JoseSanchez122/MULTI_TIMERS_CALIBRATOR/Hardware_design/parts/3D/BUTTON_TL3301FF160QG.step

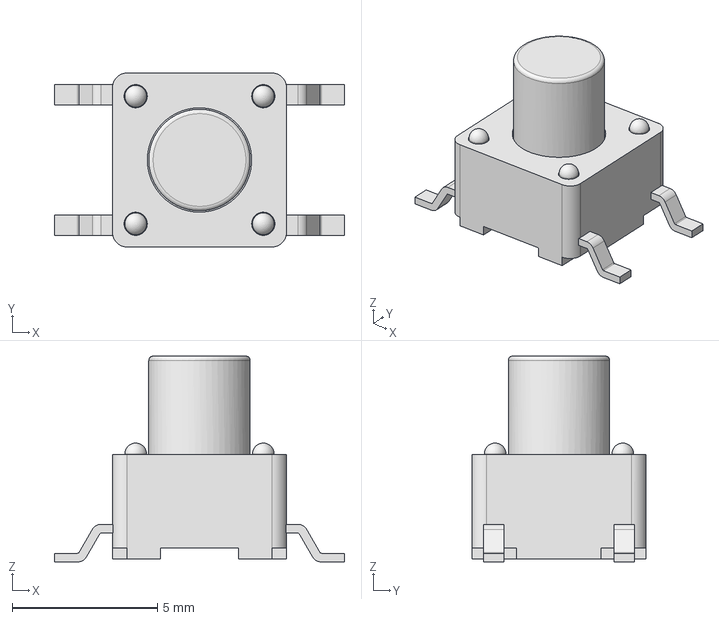
[picture p16: CAD file, 2026-05-31]
Hardware_design/parts/3D/BUTTON_TL3301FF160QG.step
10.0 x 6.00 x 7.10 mm
