JoseSanchez122/MULTI_TIMERS_CALIBRATOR/Hardware_design/parts/3D/V_REGU_LP3875EMP-3.3.step

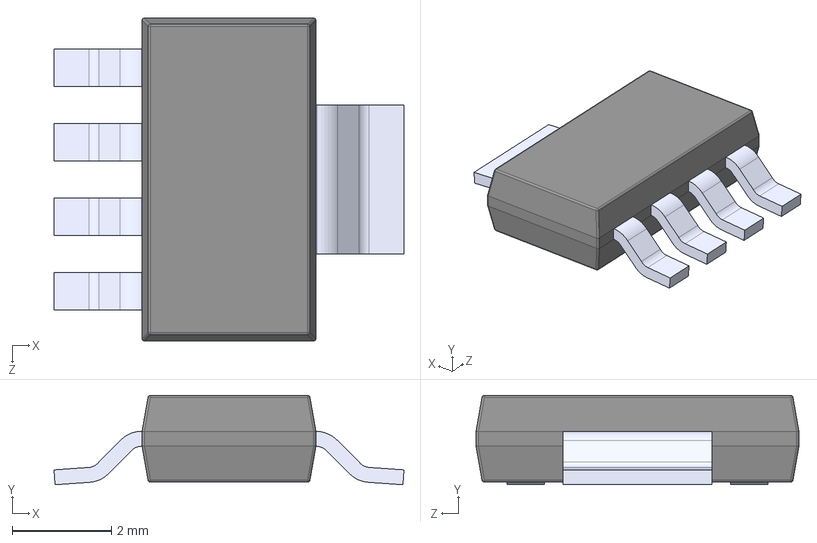
[picture p17: CAD file, 2026-05-31]
Hardware_design/parts/3D/V_REGU_LP3875EMP-3.3.step
7.04 x 1.80 x 6.50 mm
