JoseSanchez122/MULTI_TIMERS_CALIBRATOR/Hardware_design/parts/3D/LS7366R-S.step

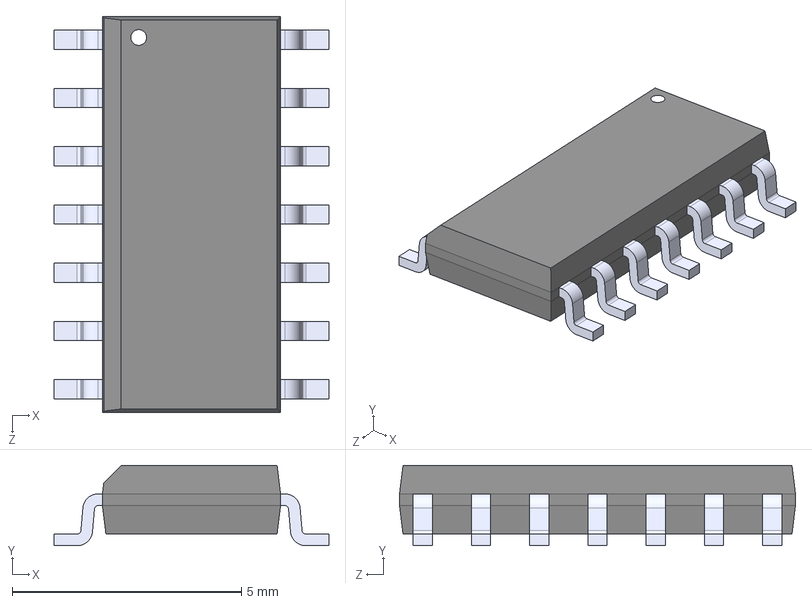
[picture p18: CAD file, 2026-05-31]
Hardware_design/parts/3D/LS7366R-S.step
5.99 x 1.75 x 8.64 mm
