JoseSanchez122/MULTI_TIMERS_CALIBRATOR/Hardware_design/parts/3D/POWER_CONE_54-00131.step

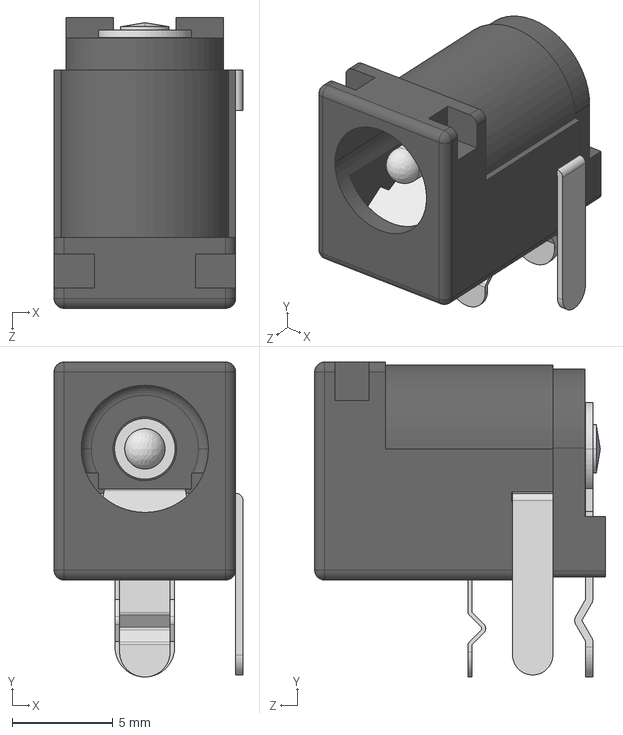
[picture p19: CAD file, 2026-05-31]
Hardware_design/parts/3D/POWER_CONE_54-00131.step
9.36 x 15.6 x 14.4 mm
