JoseSanchez122/MULTI_TIMERS_CALIBRATOR/Hardware_design/parts/3D/GREEN_LED_LTST-C170KGKT.step

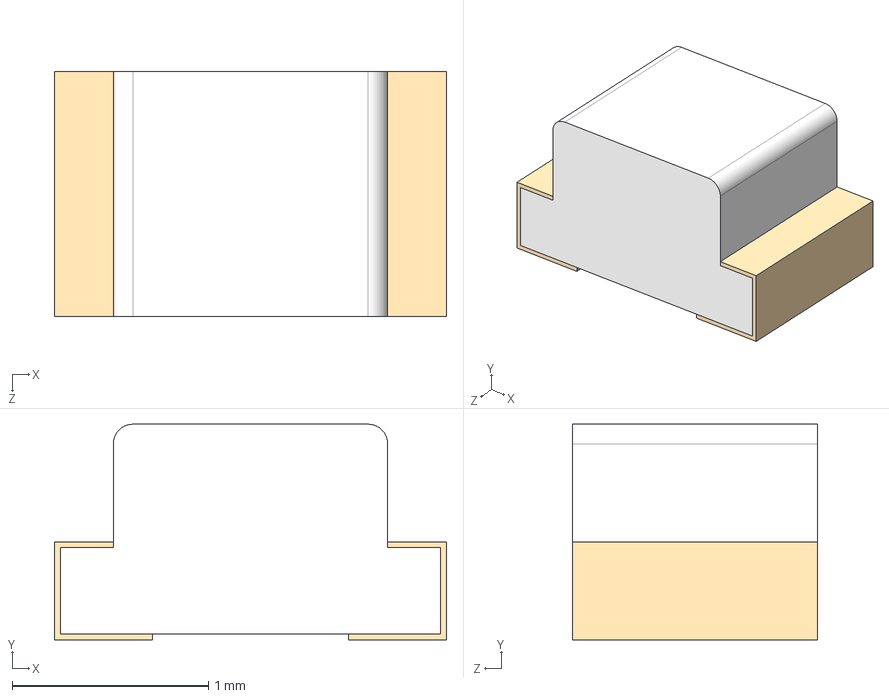
[picture p20: CAD file, 2026-05-31]
Hardware_design/parts/3D/GREEN_LED_LTST-C170KGKT.step
2.00 x 1.10 x 1.25 mm
