JoseSanchez122/MULTI_TIMERS_CALIBRATOR/Hardware_design/parts/3D/DEBOUNCE_CHIP_SN74LVC1G123DCTR.step

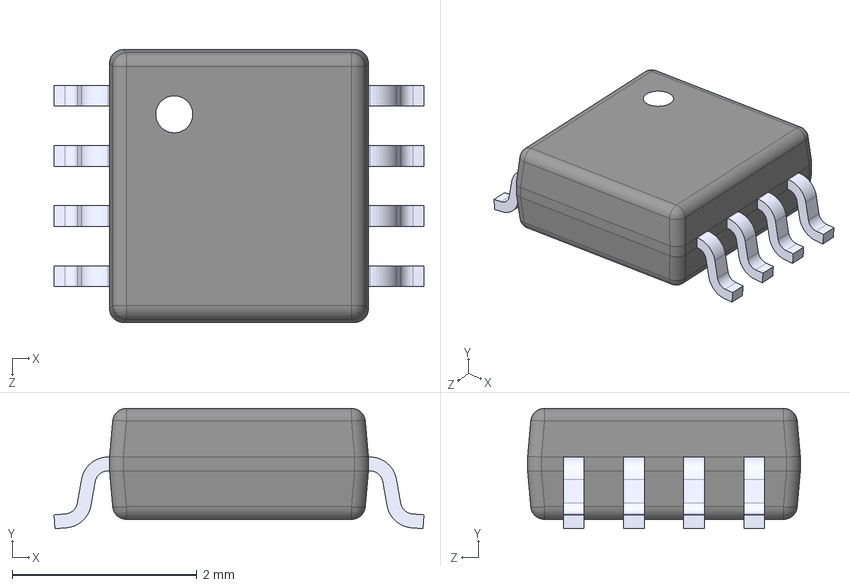
[picture p21: CAD file, 2026-05-31]
Hardware_design/parts/3D/DEBOUNCE_CHIP_SN74LVC1G123DCTR.step
4.00 x 1.30 x 2.95 mm
