JoseSanchez122/MULTI_TIMERS_CALIBRATOR/Hardware_design/parts/3D/PROG_CONECTOR_FTSH-103-01-F-D.step

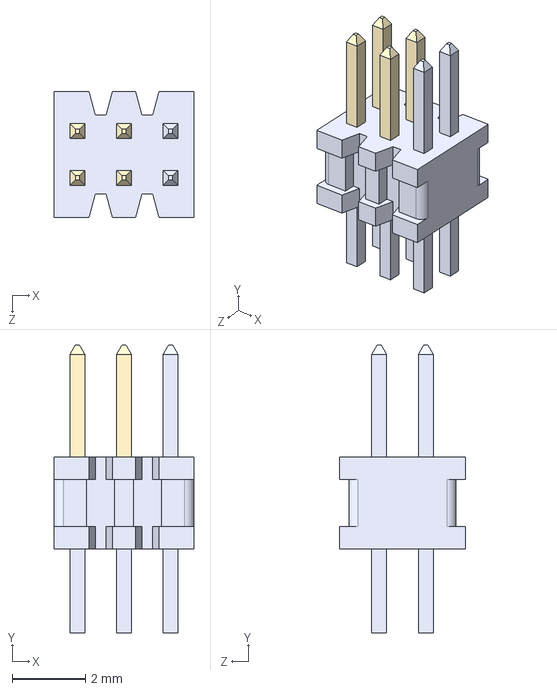
[picture p22: CAD file, 2026-05-31]
Hardware_design/parts/3D/PROG_CONECTOR_FTSH-103-01-F-D.step
3.81 x 7.85 x 3.43 mm
