JoseSanchez122/MULTI_TIMERS_CALIBRATOR/Hardware_design/parts/3D/ESP32-S3-WROOM-1-N16.stp

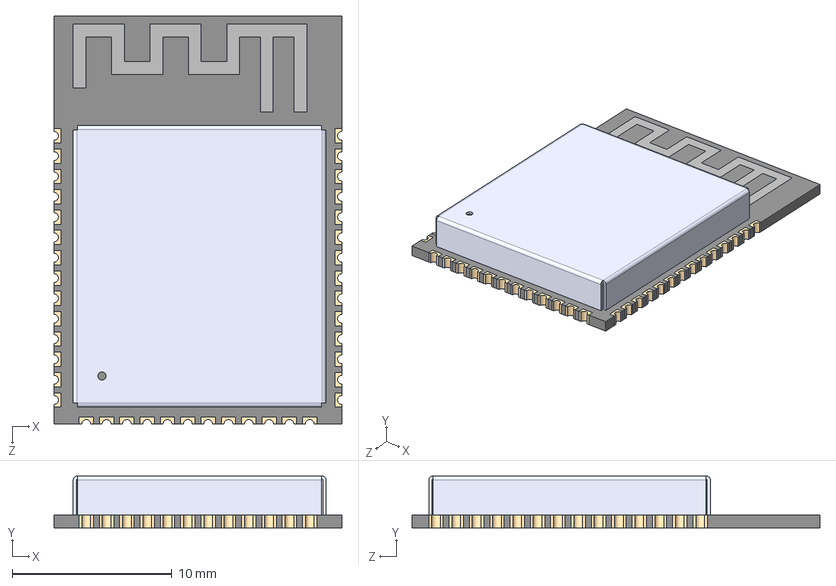
[picture p23: CAD file, 2026-05-30]
Hardware_design/parts/3D/ESP32-S3-WROOM-1-N16.stp
18.0 x 3.25 x 25.5 mm
