JoseSanchez122/MULTI_TIMERS_CALIBRATOR/Hardware_design/Hardware_design.kicad_pcb

## KiCad design Hardware_design/Hardware_design.kicad_pcb (2026-07-23)

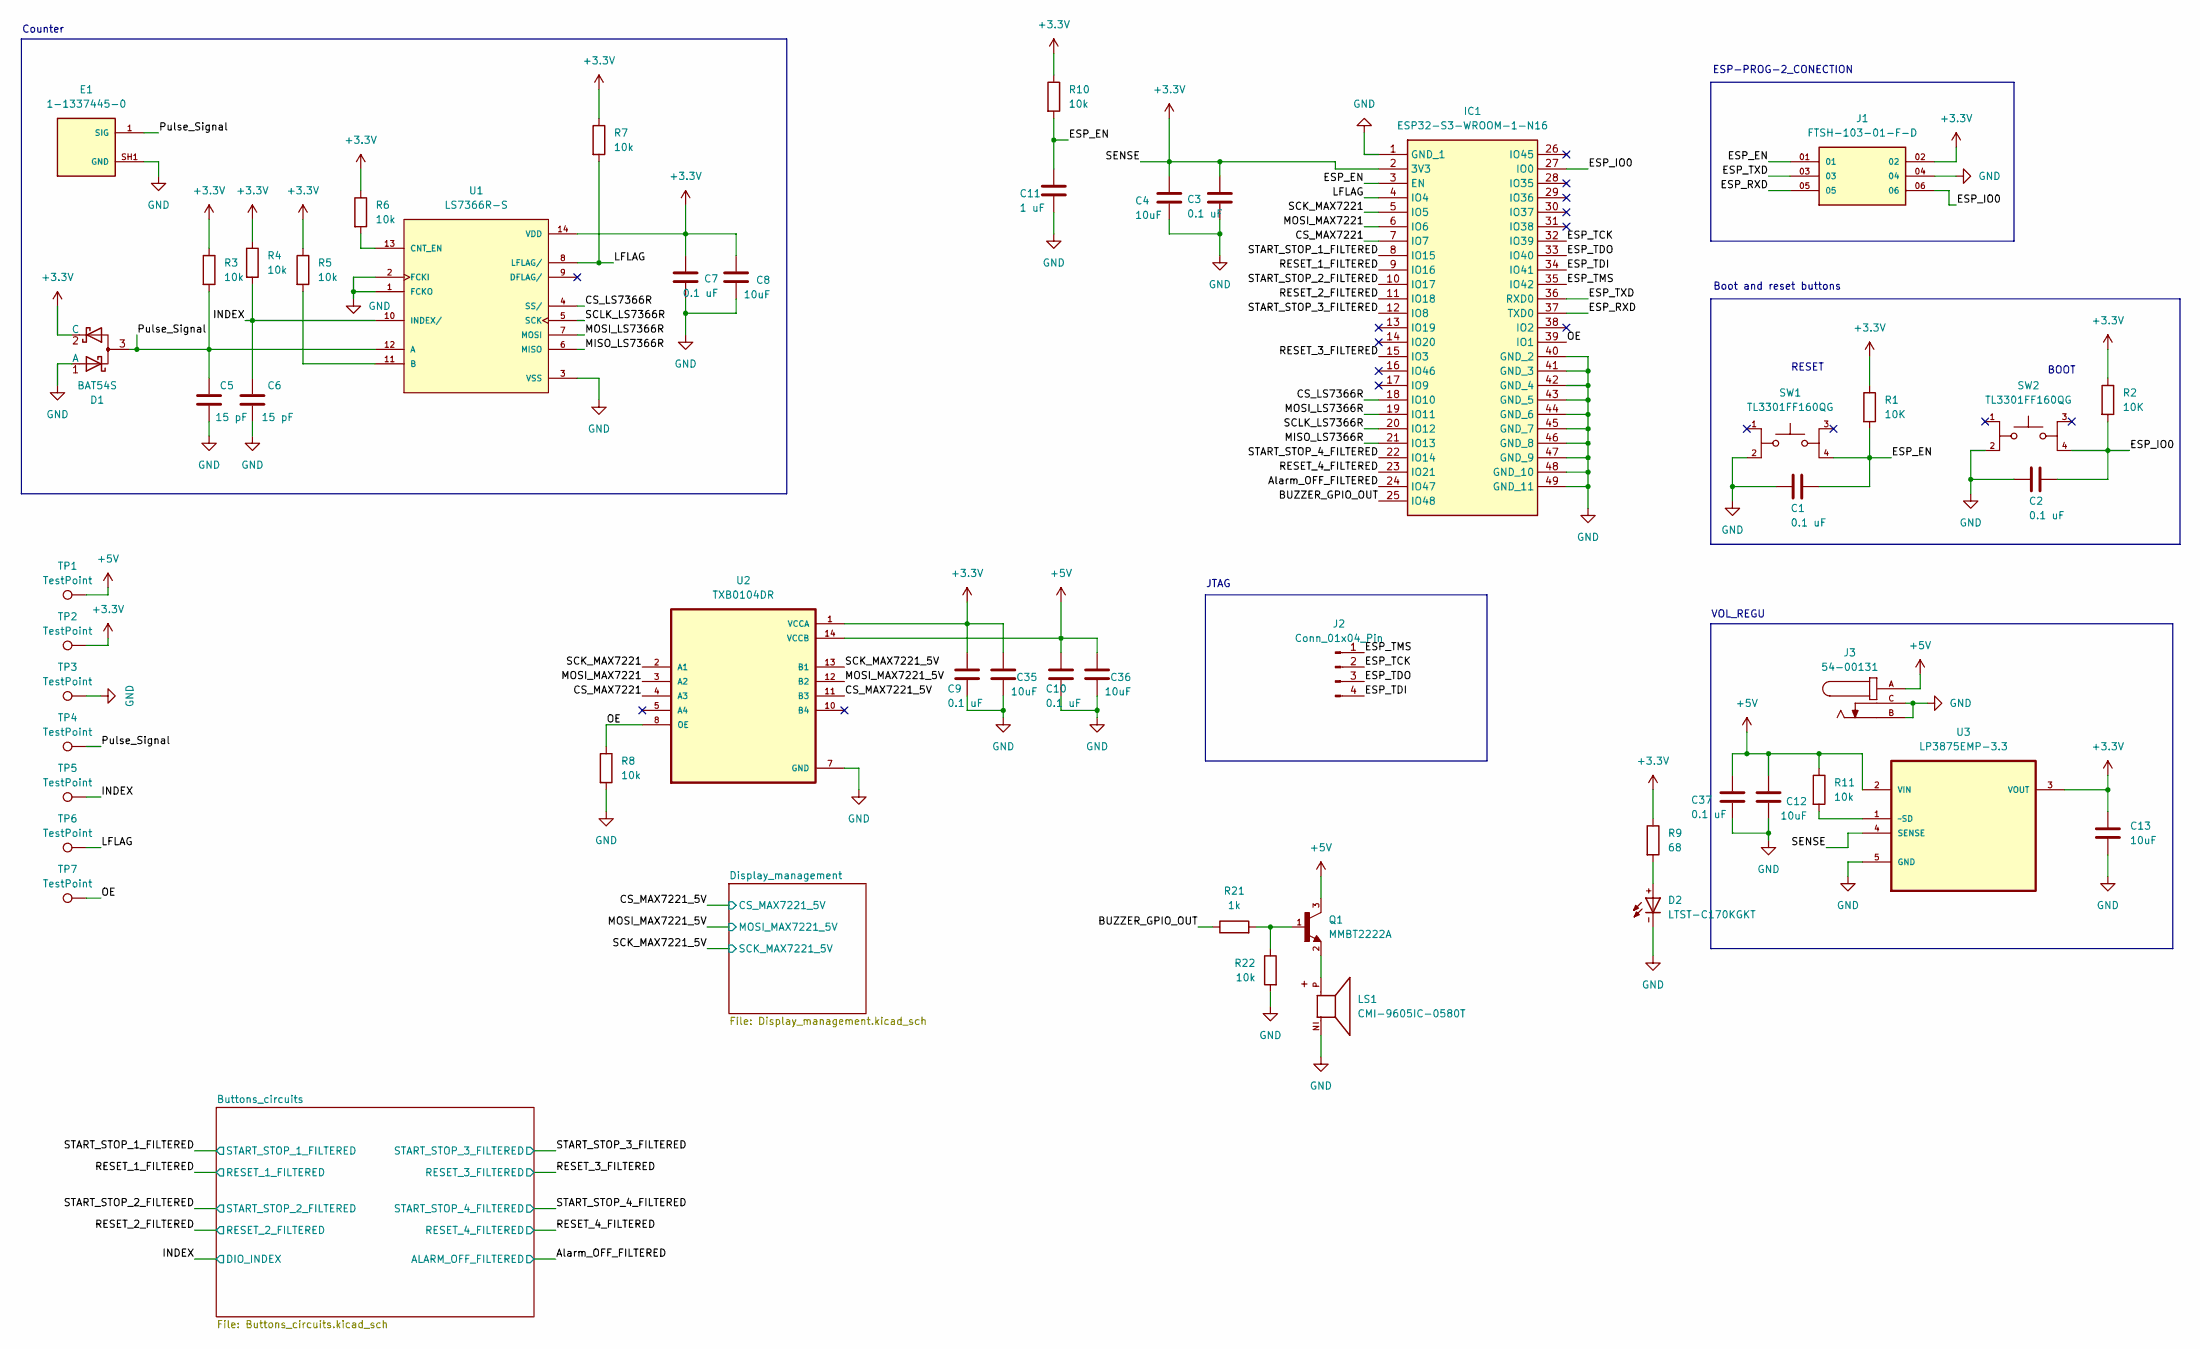
[picture p24: schematic Hardware_design.kicad_sch]

Parts:
C1, C2, C3, C7, C9, C10, C37: 0.1 uF; 0805_SMD_CERAMIC_CAP_T491B106K016AT
C4, C8, C12, C13, C35, C36: 10uF; 0805_SMD_TANT_CAP_T491B106K016AT
C5, C6: 15 pF; 0805_SMD_CERAMIC_CAP_T491B106K016AT
C11: 1 uF; CAP_0603_CAPC1608X90N
D1: BAT54S; Schottky_diode_BAT54S
D2: LTST-C170KGKT; GREEN_LED_LTST-C170KGKT; DigiKey_Part_Number 160-1414-1-ND
E1: 1-1337445-0; VNC_CONECTOR_1-1337445-0; PARTREV C
IC1: ESP32-S3-WROOM-1-N16; ESP32S3WROOM1N16; Mouser Part Number 356-ESP32S3WROOM1N16
J1: FTSH-103-01-F-D; PROG_CONECTOR_SAMTEC_FTSH-103-01-F-D; PARTREV B
J2: Conn_01x04_Pin; 4_pin_FTR-104-01-L-S
J3: 54-00131; POWER_CONE_54-00131; PARTREV A
LS1: CMI-9605IC-0580T; BUZZER_CMI-9605IC-0580T; PARTREV 1.0
Q1: MMBT2222A; TRANSISTOR_MMBT2222A; PARTREV 2024-03-11
R1, R2: 10K; 0805_RES_RESC2012X60N
R3, R4, R5, R6, R7, R8, R10, R11, R22: 10k; 0805_RES_RESC2012X60N
R9: 68; 0805_RES_RESC2012X60N
R21: 1k; 0805_RES_RESC2012X60N
SW1, SW2: TL3301FF160QG; BUTTON_TL3301FF160QG; PARTREV E
TP1, TP2, TP3, TP4, TP5, TP6, TP7: TestPoint; TestPoint_Pad_1.0x1.0mm
U1: LS7366R-S; PARTREV June 2014
U2: TXB0104DR; LEVEL_SHIFTER_TXB0104DR
U3: LP3875EMP-3.3; V_REGU_LP3875EMP-3.3; MPN LP3875EMP-3.3

Connections:
+3.3V: C3.1, C4.1, C7.1, C8.1, C9.1, C13.1, C35.1, D1.2 (C), IC1.2 (3V3), J1.02, R1.1, R2.1, R3.1, R4.1, R5.1, R6.1, R7.1, R9.1, R10.1, TP2.1 (1_1), U1.14 (VDD), U2.1 (VCCA), U3.3 (VOUT), U3.4 (SENSE); also elsewhere on the board
+5V: C10.1, C12.1, C36.1, C37.1, J3.A, Q1.3, R11.1, TP1.1 (1_1), U2.14 (VCCB), U3.2 (VIN); also elsewhere on the board
/Alarm_OFF_FILTERED: IC1.24 (IO47); also elsewhere on the board
/BUZZER_GPIO_OUT: IC1.25 (IO48), R21.1
/CS_LS7366R: IC1.18 (IO10), U1.4 (SS/)
/CS_MAX7221: IC1.7 (IO7), U2.4 (A3)
/CS_MAX7221_5V: U2.11 (B3); also elsewhere on the board
/ESP_EN: C1.1, C11.1, IC1.3 (EN), J1.01, R1.2, R10.2, SW1.4
/ESP_IO0: C2.1, IC1.27 (IO0), J1.06, R2.2, SW2.4
/ESP_RXD: IC1.37 (TXD0), J1.05
/ESP_TCK: IC1.32 (IO39), J2.2
/ESP_TDI: IC1.34 (IO41), J2.4
/ESP_TDO: IC1.33 (IO40), J2.3
/ESP_TMS: IC1.35 (IO42), J2.1
/ESP_TXD: IC1.36 (RXD0), J1.03
/INDEX: C6.1, R4.2, TP5.1 (1_1), U1.10 (INDEX/); also elsewhere on the board
/LFLAG: IC1.4 (IO4), R7.2, TP6.1 (1_1), U1.8 (LFLAG/)
/MISO_LS7366R: IC1.21 (IO13), U1.6 (MISO)
/MOSI_LS7366R: IC1.19 (IO11), U1.7 (MOSI)
/MOSI_MAX7221: IC1.6 (IO6), U2.3 (A2)
/MOSI_MAX7221_5V: U2.12 (B2); also elsewhere on the board
/OE: IC1.39 (IO1), R8.1, TP7.1 (1_1), U2.8 (OE)
/Pulse_Signal: C5.1, D1.3, E1.1 (SIG), R3.2, TP4.1 (1_1), U1.12 (A)
/RESET_1_FILTERED: IC1.9 (IO16); also elsewhere on the board
/RESET_2_FILTERED: IC1.11 (IO18); also elsewhere on the board
/RESET_3_FILTERED: IC1.15 (IO3); also elsewhere on the board
/RESET_4_FILTERED: IC1.23 (IO21); also elsewhere on the board
/SCK_MAX7221: IC1.5 (IO5), U2.2 (A1)
/SCK_MAX7221_5V: U2.13 (B1); also elsewhere on the board
/SCLK_LS7366R: IC1.20 (IO12), U1.5 (SCK)
/START_STOP_1_FILTERED: IC1.8 (IO15); also elsewhere on the board
/START_STOP_2_FILTERED: IC1.10 (IO17); also elsewhere on the board
/START_STOP_3_FILTERED: IC1.12 (IO8); also elsewhere on the board
/START_STOP_4_FILTERED: IC1.22 (IO14); also elsewhere on the board
GND: C1.2, C2.2, C3.2, C4.2, C5.2, C6.2, C7.2, C8.2, C9.2, C10.2, C11.2, C12.2, C13.2, C35.2, C36.2, C37.2, D1.1 (A), D2.-, E1.SH1 (GND), E1.SH2 (GND), E1.SH3 (GND), E1.SH4 (GND), IC1.1 (GND_1), IC1.40 (GND_2), IC1.41 (GND_3), IC1.42 (GND_4), IC1.43 (GND_5), IC1.44 (GND_6), IC1.45 (GND_7), IC1.46 (GND_8), IC1.47 (GND_9), IC1.48 (GND_10), IC1.49 (GND_11), J1.04, J3.B, J3.C, LS1.N, R8.2, R22.2, SW1.2, SW2.2, TP3.1 (1_1), U1.1 (FCKO), U1.2 (FCKI), U1.3 (VSS), U2.7 (GND), U3.5 (GND); also elsewhere on the board
unnamed: D2.+, R9.2
unnamed: LS1.P, Q1.2
unnamed: Q1.1, R21.2, R22.1
unnamed: R5.2, U1.11 (B)
unnamed: R6.2, U1.13 (CNT_EN)
unnamed: R11.2, U3.1 (~SD)

Notes on the sheet:
BOOT
Boot and reset buttons
VOL_REGU
ESP-PROG-2_CONECTION
RESET
Counter
JTAG
