JoseSanchez122/MULTI_TIMERS_CALIBRATOR/Hardware_design/Hardware_design.kicad_pcb

## KiCad design Hardware_design/Hardware_design.kicad_pcb (continued)

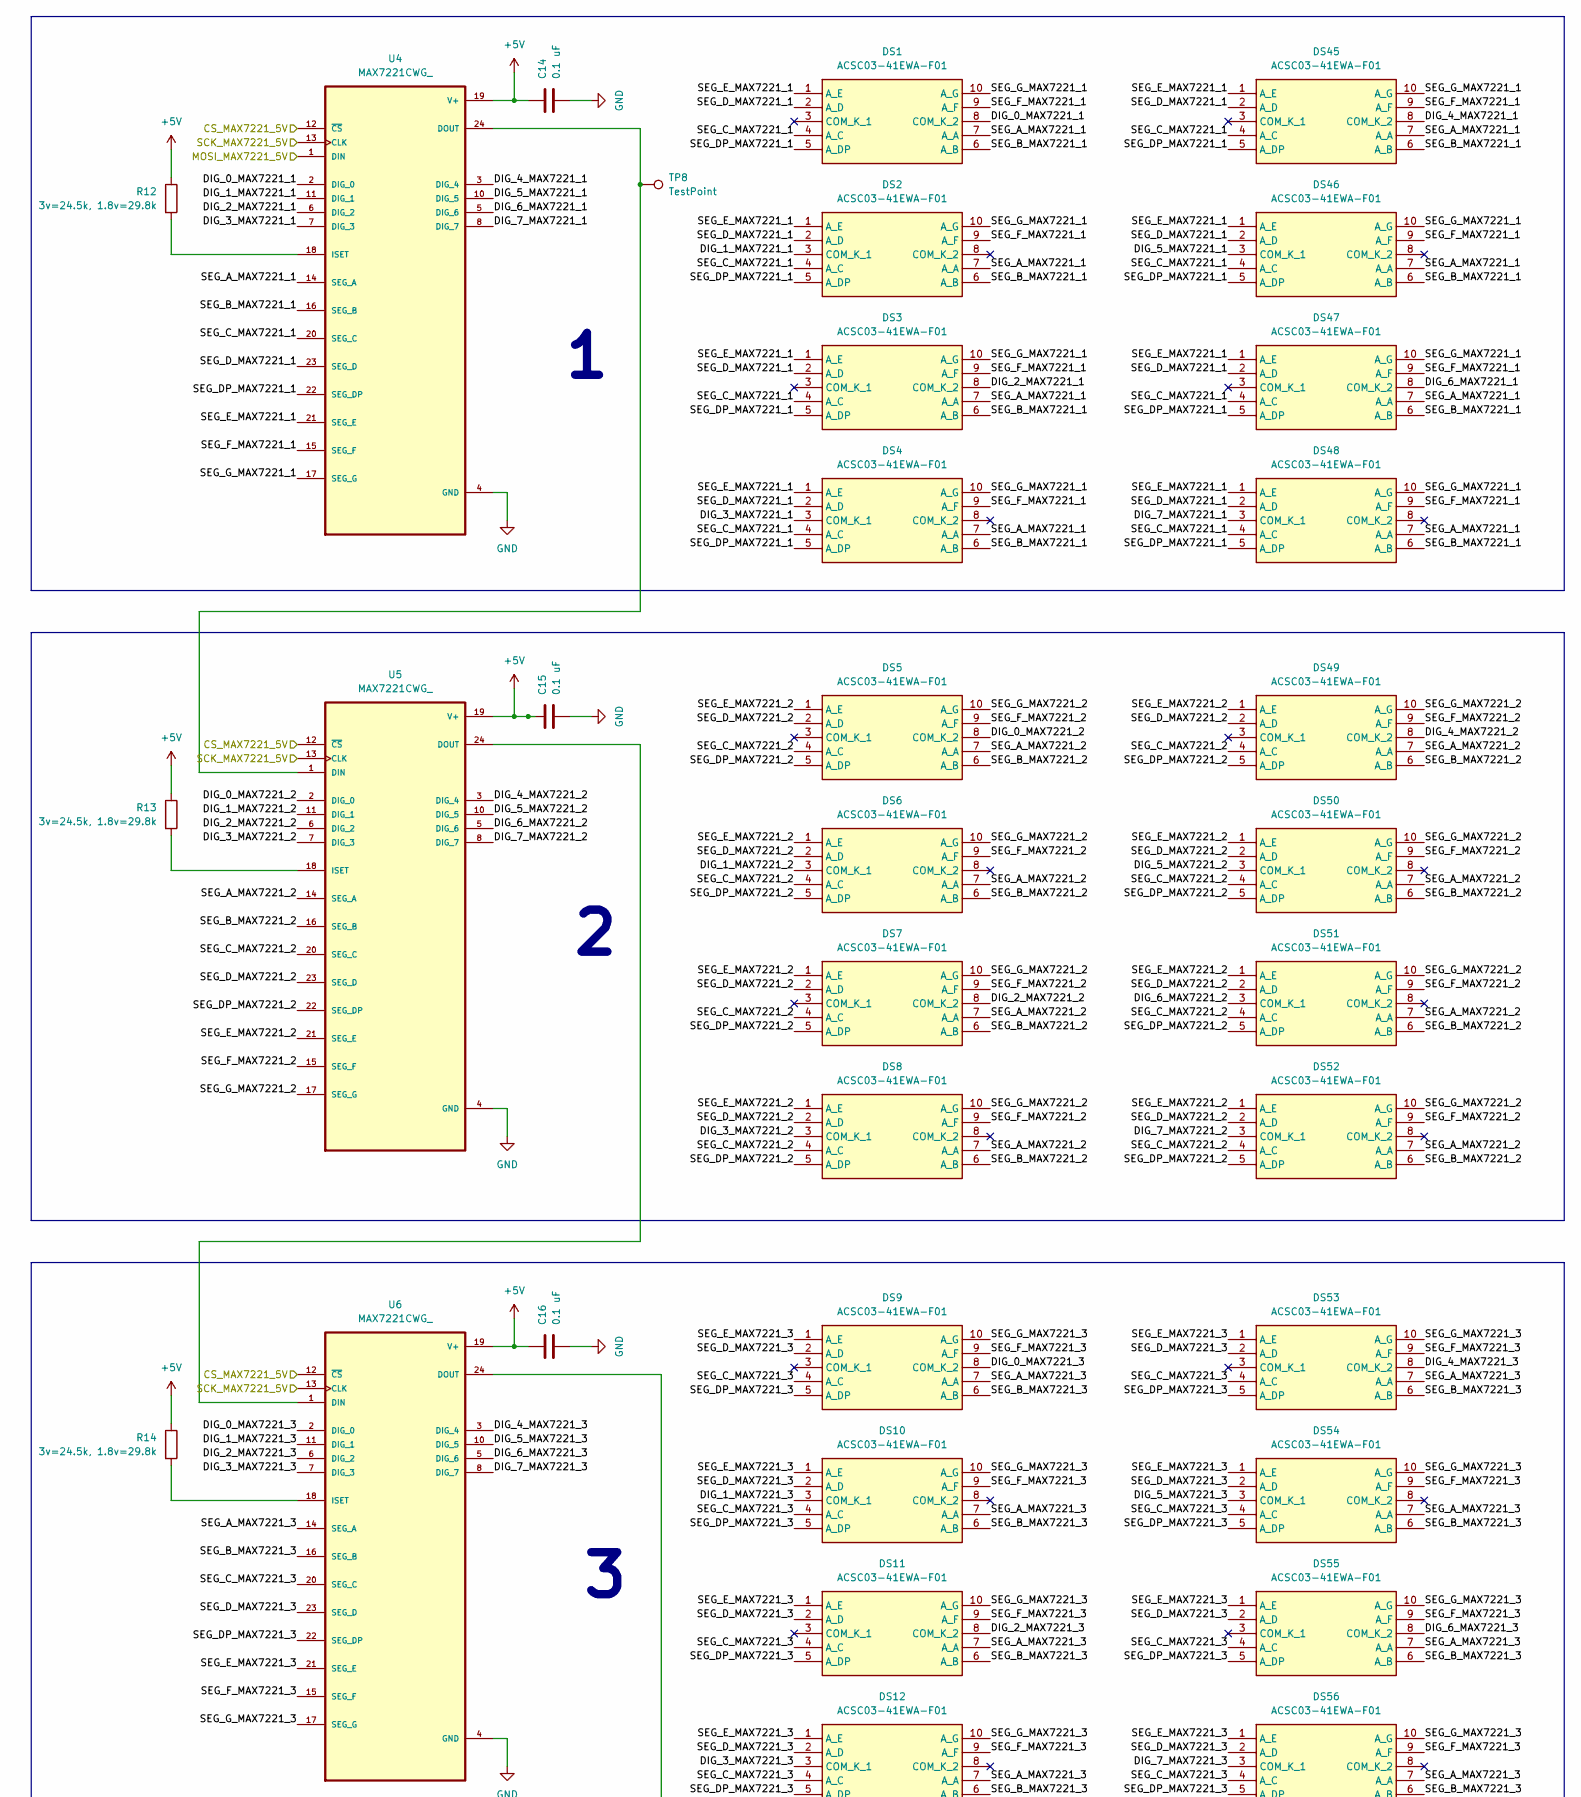
[picture p25: schematic Display_management.kicad_sch, part in row 1, column 1]

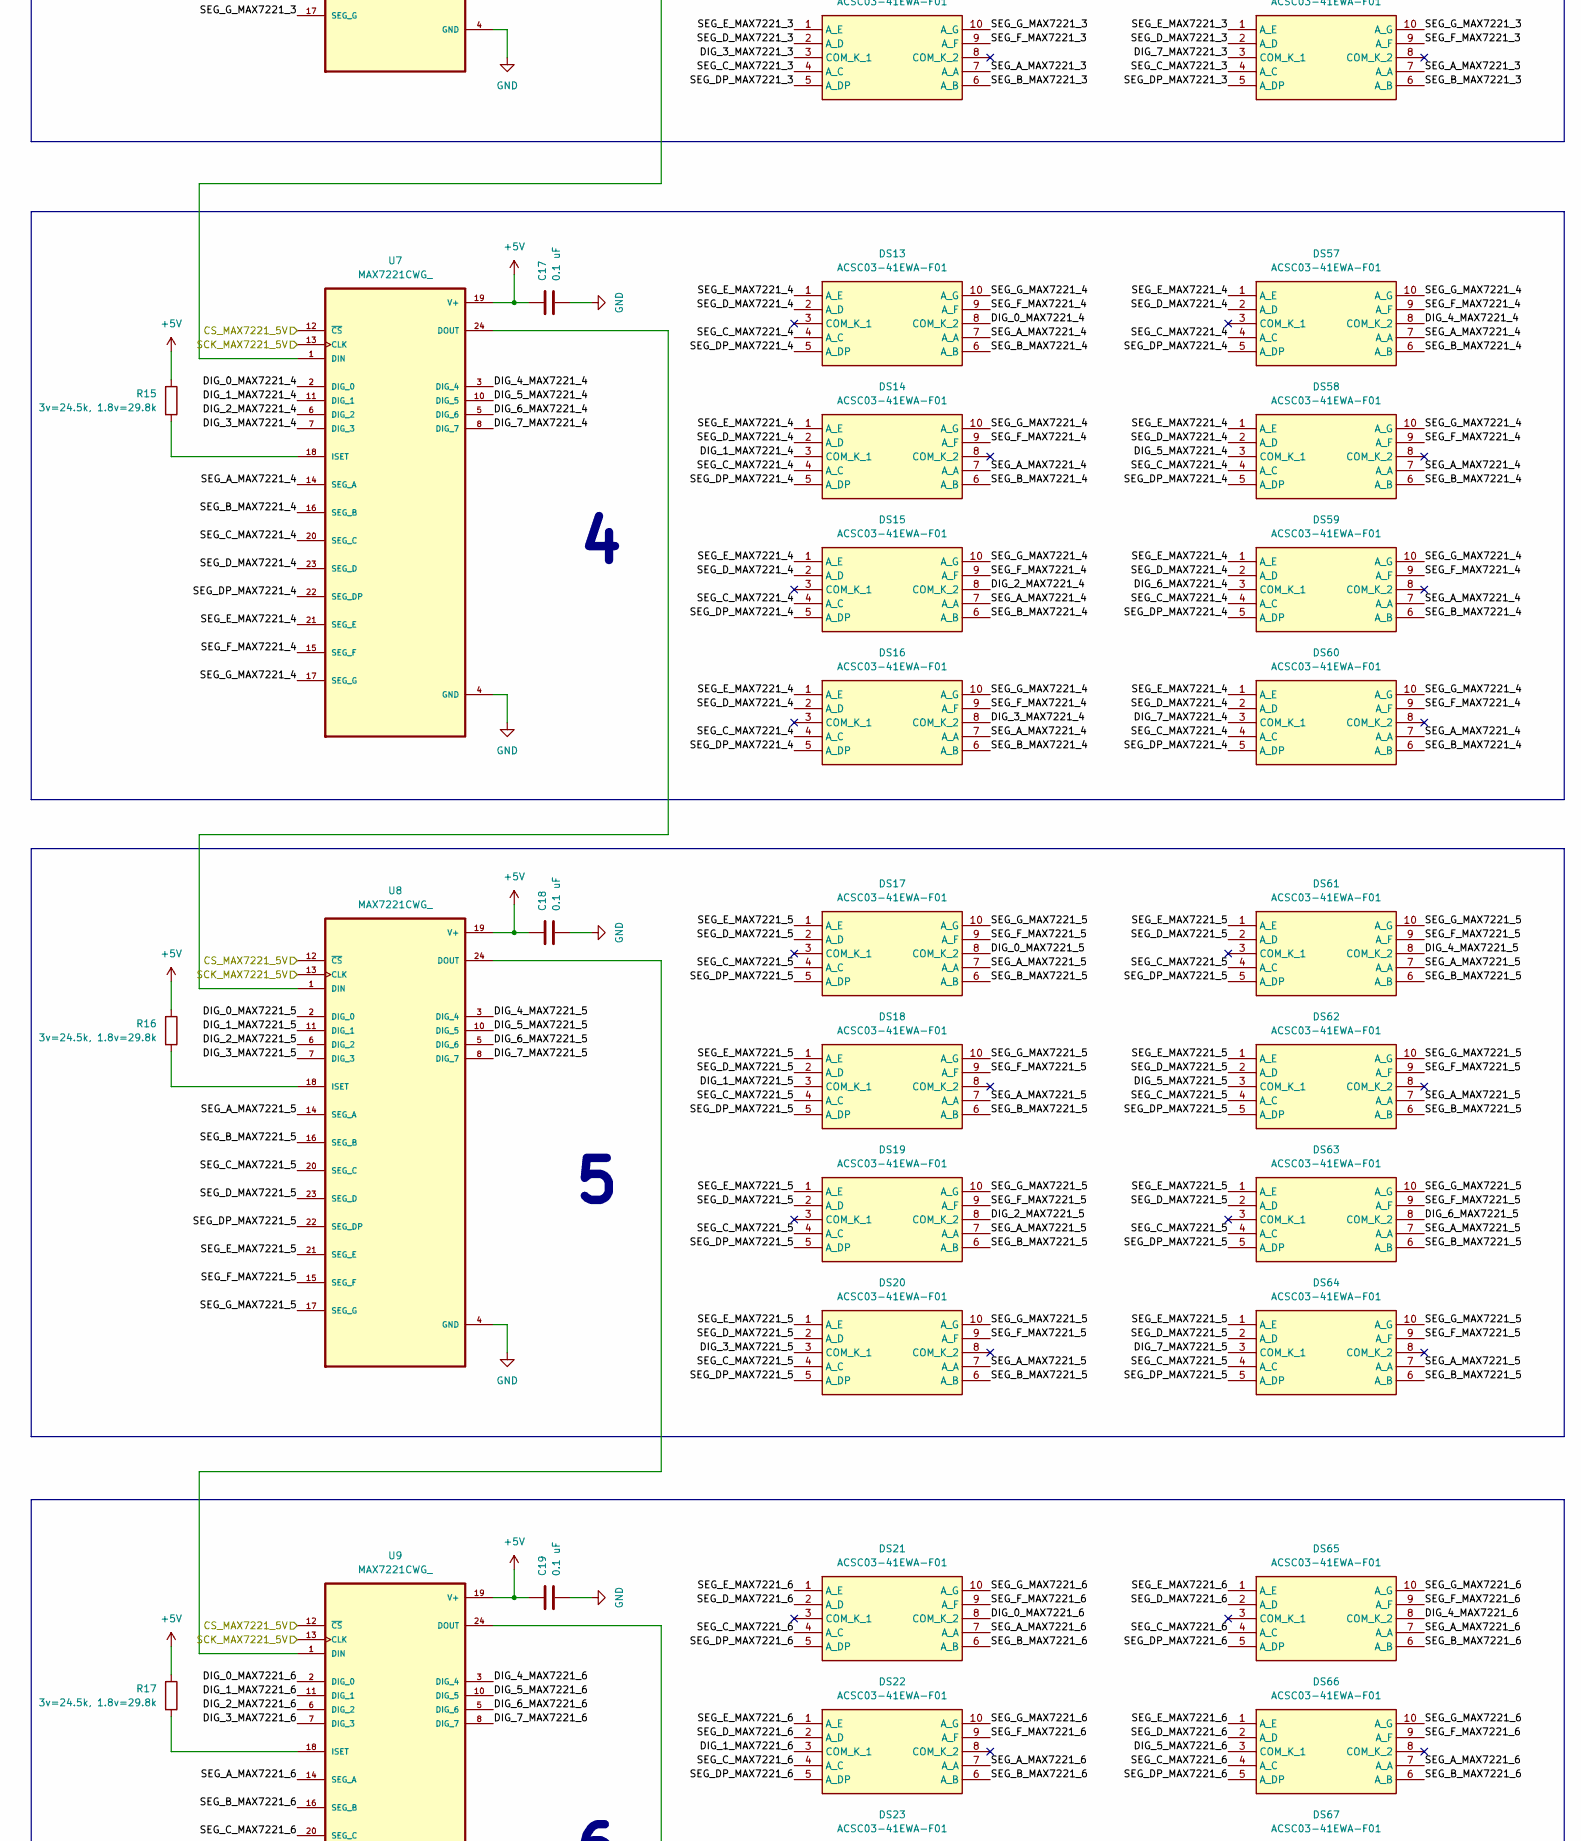
[picture p26: schematic Display_management.kicad_sch, part in row 2, column 1]

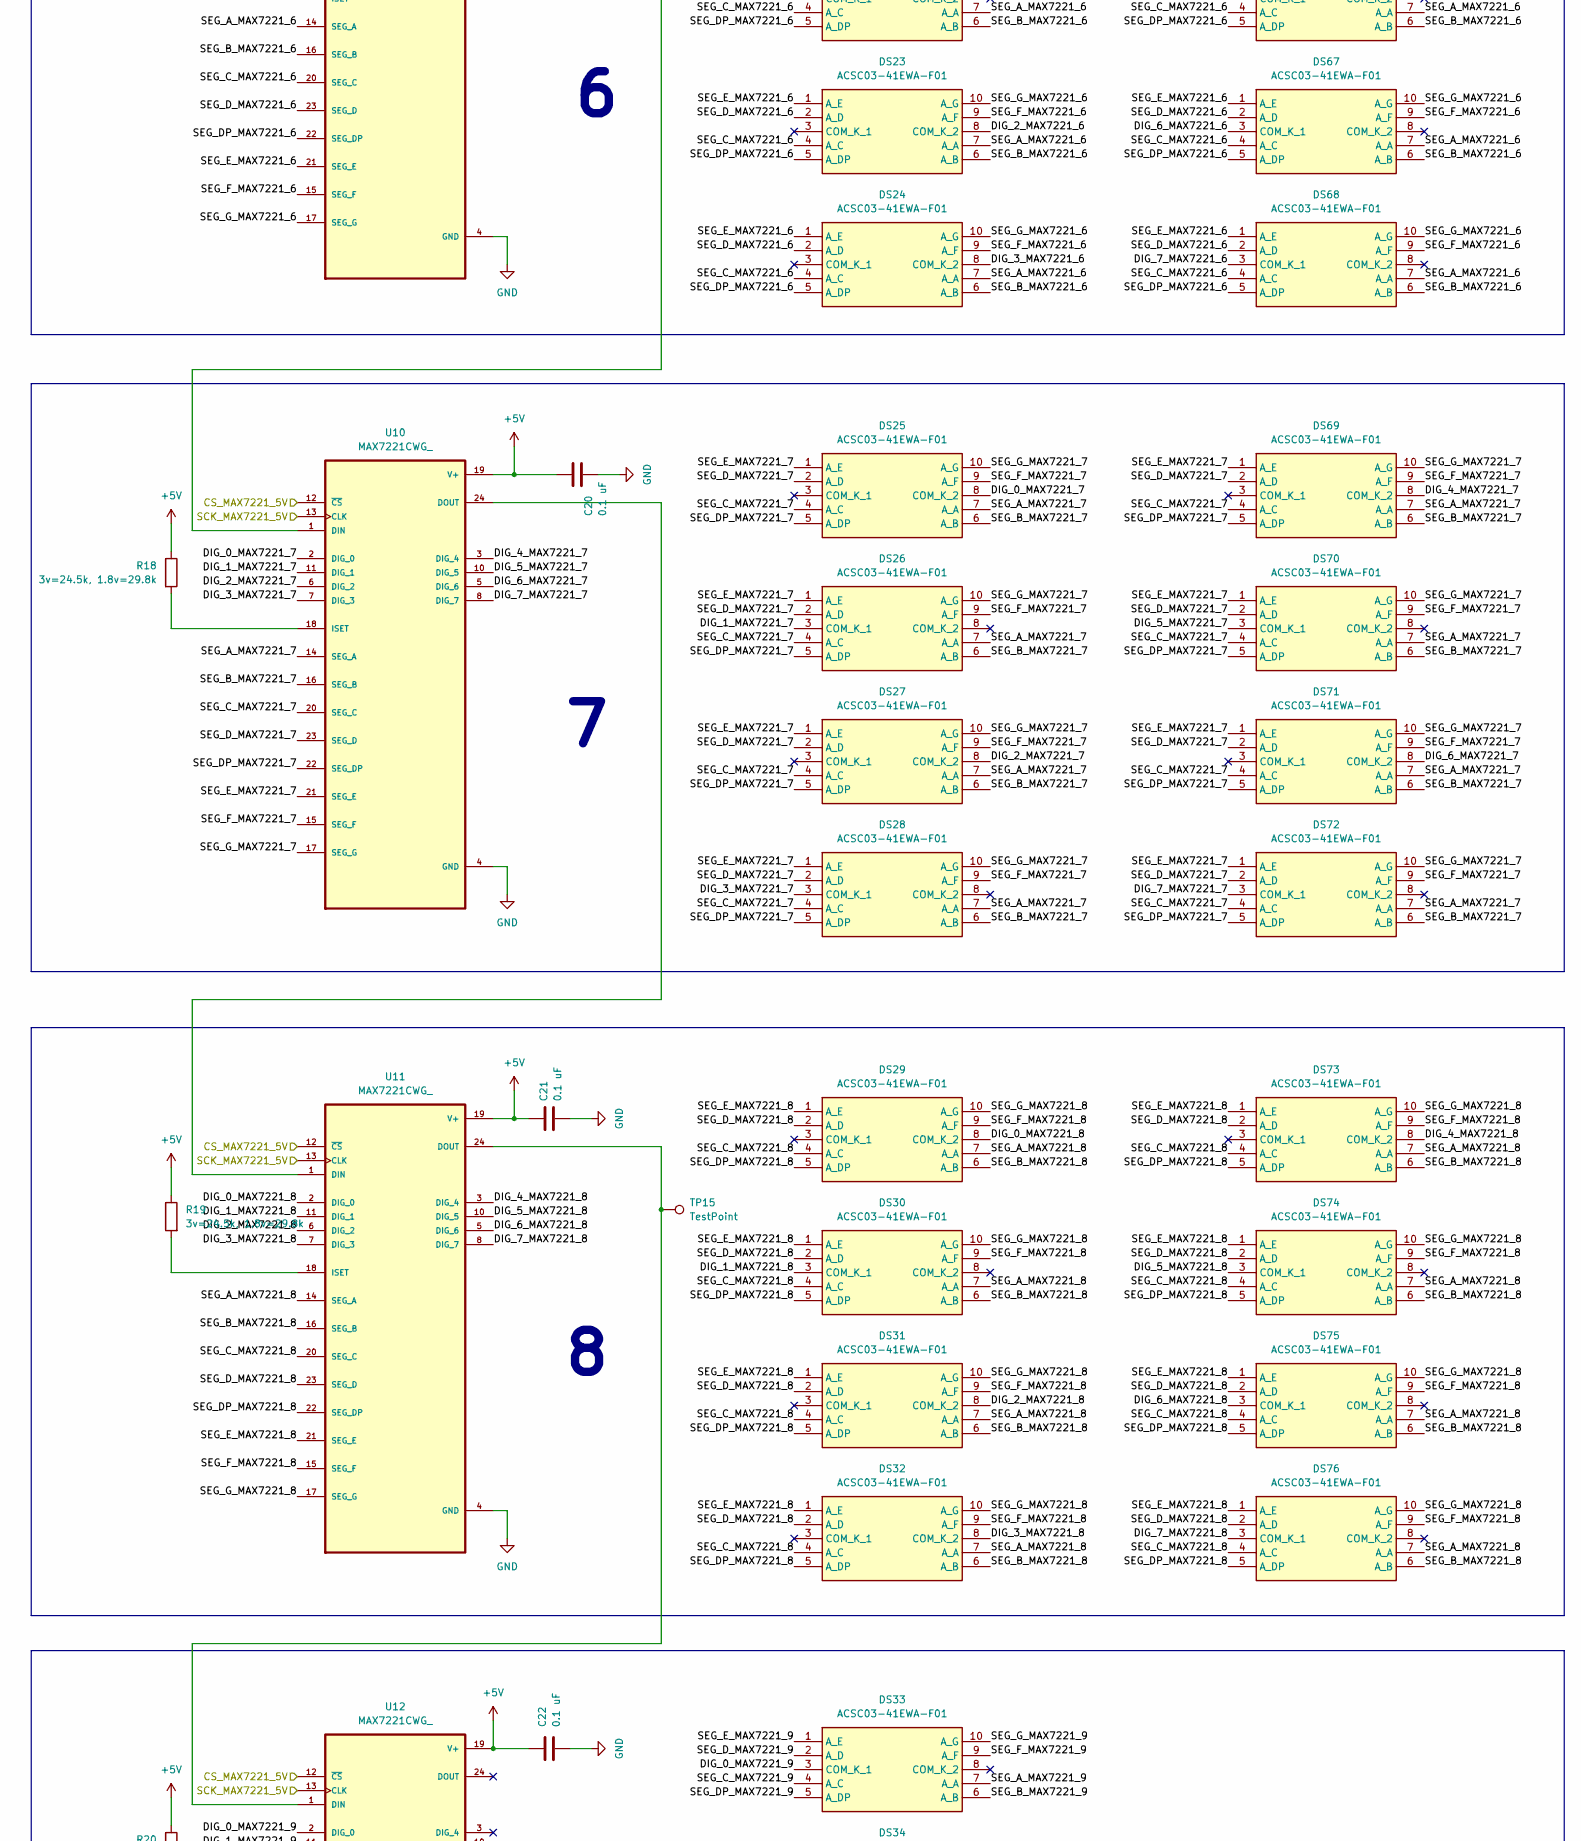
[picture p27: schematic Display_management.kicad_sch, part in row 3, column 1]

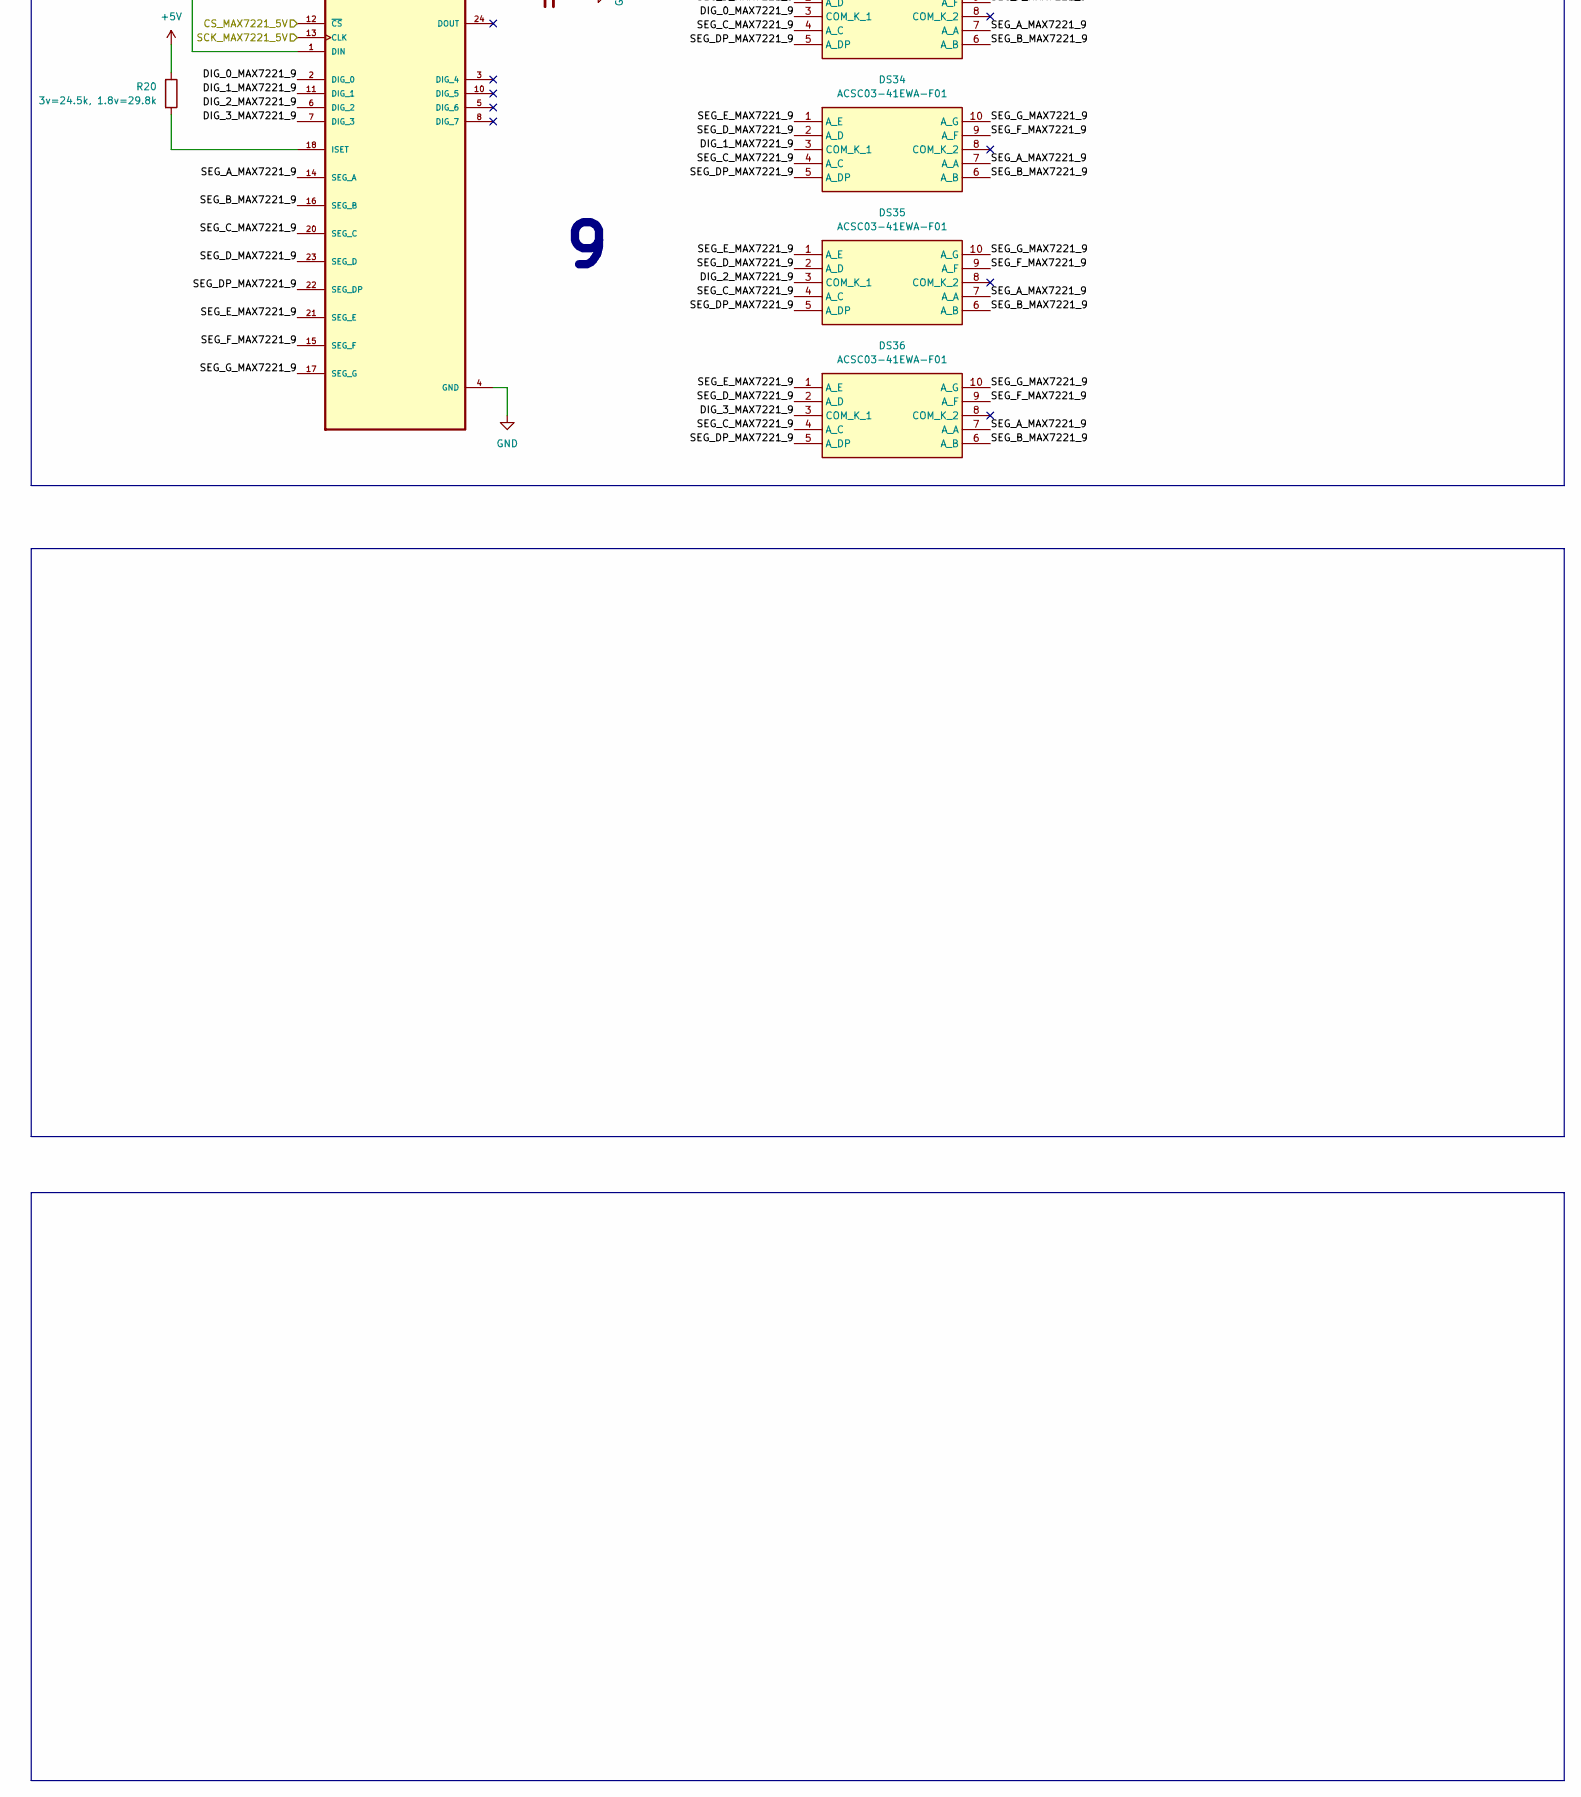
[picture p28: schematic Display_management.kicad_sch, part in row 4, column 1]

Parts:
C14, C15, C16, C17, C18, C19, C20, C21, C22: 0.1 uF; 0805_SMD_CERAMIC_CAP_T491B106K016AT
DS1, DS2, DS3, DS4, DS5, DS6, DS7, DS8, DS9, DS10, DS11, DS12, DS13, DS14, DS15, DS16, DS17, DS18, DS19, DS20, DS21, DS22, DS23, DS24, DS25, DS26, DS27, DS28, DS29, DS30, DS31, DS32, DS33, DS34, DS35, DS36, DS45, DS46, DS47, DS48, DS49, DS50, DS51, DS52, DS53, DS54, DS55, DS56, DS57, DS58, DS59, DS60, DS61, DS62, DS63, DS64, DS65, DS66, DS67, DS68, DS69, DS70, DS71, DS72, DS73, DS74, DS75, DS76: ACSC03-41EWA-F01; SMD_DISPLAY_ACSC03-41EWA-F01; Mouser Part Number 604-ACSC03-41EWA-F01
R12, R13, R14, R15, R16, R17, R18, R19, R20: 3v=24.5k, 1.8v=29.8k; 0805_RES_RESC2012X60N
TP8, TP15: TestPoint; TestPoint_Pad_1.0x1.0mm
U4, U5, U6, U7, U8, U9, U10, U11, U12: MAX7221CWG_; Disp_Controler_MAX7221CWG_

Connections:
+5V: C14.1, C15.1, C16.1, C17.1, C18.1, C19.1, C20.1, C21.1, C22.1, R12.1, R13.1, R14.1, R15.1, R16.1, R17.1, R18.1, R19.1, R20.1, U4.19 (V+), U5.19 (V+), U6.19 (V+), U7.19 (V+), U8.19 (V+), U9.19 (V+), U10.19 (V+), U11.19 (V+), U12.19 (V+); also elsewhere on the board
/CS_MAX7221_5V: U4.12 (~CS), U5.12 (~CS), U6.12 (~CS), U7.12 (~CS), U8.12 (~CS), U9.12 (~CS), U10.12 (~CS), U11.12 (~CS), U12.12 (~CS); also elsewhere on the board
/Display_management/DIG_0_MAX7221_1: DS1.8 (COM_K_2), U4.2 (DIG_0)
/Display_management/DIG_0_MAX7221_2: DS5.8 (COM_K_2), U5.2 (DIG_0)
/Display_management/DIG_0_MAX7221_3: DS9.8 (COM_K_2), U6.2 (DIG_0)
/Display_management/DIG_0_MAX7221_4: DS13.8 (COM_K_2), U7.2 (DIG_0)
/Display_management/DIG_0_MAX7221_5: DS17.8 (COM_K_2), U8.2 (DIG_0)
/Display_management/DIG_0_MAX7221_6: DS21.8 (COM_K_2), U9.2 (DIG_0)
/Display_management/DIG_0_MAX7221_7: DS25.8 (COM_K_2), U10.2 (DIG_0)
/Display_management/DIG_0_MAX7221_8: DS29.8 (COM_K_2), U11.2 (DIG_0)
/Display_management/DIG_0_MAX7221_9: DS33.3 (COM_K_1), U12.2 (DIG_0)
/Display_management/DIG_1_MAX7221_1: DS2.3 (COM_K_1), U4.11 (DIG_1)
/Display_management/DIG_1_MAX7221_2: DS6.3 (COM_K_1), U5.11 (DIG_1)
/Display_management/DIG_1_MAX7221_3: DS10.3 (COM_K_1), U6.11 (DIG_1)
/Display_management/DIG_1_MAX7221_4: DS14.3 (COM_K_1), U7.11 (DIG_1)
/Display_management/DIG_1_MAX7221_5: DS18.3 (COM_K_1), U8.11 (DIG_1)
/Display_management/DIG_1_MAX7221_6: DS22.3 (COM_K_1), U9.11 (DIG_1)
/Display_management/DIG_1_MAX7221_7: DS26.3 (COM_K_1), U10.11 (DIG_1)
/Display_management/DIG_1_MAX7221_8: DS30.3 (COM_K_1), U11.11 (DIG_1)
/Display_management/DIG_1_MAX7221_9: DS34.3 (COM_K_1), U12.11 (DIG_1)
/Display_management/DIG_2_MAX7221_1: DS3.8 (COM_K_2), U4.6 (DIG_2)
/Display_management/DIG_2_MAX7221_2: DS7.8 (COM_K_2), U5.6 (DIG_2)
/Display_management/DIG_2_MAX7221_3: DS11.8 (COM_K_2), U6.6 (DIG_2)
/Display_management/DIG_2_MAX7221_4: DS15.8 (COM_K_2), U7.6 (DIG_2)
/Display_management/DIG_2_MAX7221_5: DS19.8 (COM_K_2), U8.6 (DIG_2)
/Display_management/DIG_2_MAX7221_6: DS23.8 (COM_K_2), U9.6 (DIG_2)
/Display_management/DIG_2_MAX7221_7: DS27.8 (COM_K_2), U10.6 (DIG_2)
/Display_management/DIG_2_MAX7221_8: DS31.8 (COM_K_2), U11.6 (DIG_2)
/Display_management/DIG_2_MAX7221_9: DS35.3 (COM_K_1), U12.6 (DIG_2)
/Display_management/DIG_3_MAX7221_1: DS4.3 (COM_K_1), U4.7 (DIG_3)
/Display_management/DIG_3_MAX7221_2: DS8.3 (COM_K_1), U5.7 (DIG_3)
/Display_management/DIG_3_MAX7221_3: DS12.3 (COM_K_1), U6.7 (DIG_3)
/Display_management/DIG_3_MAX7221_4: DS16.8 (COM_K_2), U7.7 (DIG_3)
/Display_management/DIG_3_MAX7221_5: DS20.3 (COM_K_1), U8.7 (DIG_3)
/Display_management/DIG_3_MAX7221_6: DS24.8 (COM_K_2), U9.7 (DIG_3)
/Display_management/DIG_3_MAX7221_7: DS28.3 (COM_K_1), U10.7 (DIG_3)
/Display_management/DIG_3_MAX7221_8: DS32.8 (COM_K_2), U11.7 (DIG_3)
/Display_management/DIG_3_MAX7221_9: DS36.3 (COM_K_1), U12.7 (DIG_3)
/Display_management/DIG_4_MAX7221_1: DS45.8 (COM_K_2), U4.3 (DIG_4)
/Display_management/DIG_4_MAX7221_2: DS49.8 (COM_K_2), U5.3 (DIG_4)
/Display_management/DIG_4_MAX7221_3: DS53.8 (COM_K_2), U6.3 (DIG_4)
/Display_management/DIG_4_MAX7221_4: DS57.8 (COM_K_2), U7.3 (DIG_4)
/Display_management/DIG_4_MAX7221_5: DS61.8 (COM_K_2), U8.3 (DIG_4)
/Display_management/DIG_4_MAX7221_6: DS65.8 (COM_K_2), U9.3 (DIG_4)
/Display_management/DIG_4_MAX7221_7: DS69.8 (COM_K_2), U10.3 (DIG_4)
/Display_management/DIG_4_MAX7221_8: DS73.8 (COM_K_2), U11.3 (DIG_4)
/Display_management/DIG_5_MAX7221_1: DS46.3 (COM_K_1), U4.10 (DIG_5)
/Display_management/DIG_5_MAX7221_2: DS50.3 (COM_K_1), U5.10 (DIG_5)
/Display_management/DIG_5_MAX7221_3: DS54.3 (COM_K_1), U6.10 (DIG_5)
/Display_management/DIG_5_MAX7221_4: DS58.3 (COM_K_1), U7.10 (DIG_5)
/Display_management/DIG_5_MAX7221_5: DS62.3 (COM_K_1), U8.10 (DIG_5)
/Display_management/DIG_5_MAX7221_6: DS66.3 (COM_K_1), U9.10 (DIG_5)
/Display_management/DIG_5_MAX7221_7: DS70.3 (COM_K_1), U10.10 (DIG_5)
/Display_management/DIG_5_MAX7221_8: DS74.3 (COM_K_1), U11.10 (DIG_5)
/Display_management/DIG_6_MAX7221_1: DS47.8 (COM_K_2), U4.5 (DIG_6)
/Display_management/DIG_6_MAX7221_2: DS51.3 (COM_K_1), U5.5 (DIG_6)
/Display_management/DIG_6_MAX7221_3: DS55.8 (COM_K_2), U6.5 (DIG_6)
/Display_management/DIG_6_MAX7221_4: DS59.3 (COM_K_1), U7.5 (DIG_6)
/Display_management/DIG_6_MAX7221_5: DS63.8 (COM_K_2), U8.5 (DIG_6)
/Display_management/DIG_6_MAX7221_6: DS67.3 (COM_K_1), U9.5 (DIG_6)
/Display_management/DIG_6_MAX7221_7: DS71.8 (COM_K_2), U10.5 (DIG_6)
/Display_management/DIG_6_MAX7221_8: DS75.3 (COM_K_1), U11.5 (DIG_6)
/Display_management/DIG_7_MAX7221_1: DS48.3 (COM_K_1), U4.8 (DIG_7)
/Display_management/DIG_7_MAX7221_2: DS52.3 (COM_K_1), U5.8 (DIG_7)
/Display_management/DIG_7_MAX7221_3: DS56.3 (COM_K_1), U6.8 (DIG_7)
/Display_management/DIG_7_MAX7221_4: DS60.3 (COM_K_1), U7.8 (DIG_7)
/Display_management/DIG_7_MAX7221_5: DS64.3 (COM_K_1), U8.8 (DIG_7)
/Display_management/DIG_7_MAX7221_6: DS68.3 (COM_K_1), U9.8 (DIG_7)
/Display_management/DIG_7_MAX7221_7: DS72.3 (COM_K_1), U10.8 (DIG_7)
/Display_management/DIG_7_MAX7221_8: DS76.3 (COM_K_1), U11.8 (DIG_7)
/Display_management/SEG_A_MAX7221_1: DS1.7 (A_A), DS2.7 (A_A), DS3.7 (A_A), DS4.7 (A_A), DS45.7 (A_A), DS46.7 (A_A), DS47.7 (A_A), DS48.7 (A_A), U4.14 (SEG_A)
/Display_management/SEG_A_MAX7221_2: DS5.7 (A_A), DS6.7 (A_A), DS7.7 (A_A), DS8.7 (A_A), DS49.7 (A_A), DS50.7 (A_A), DS51.7 (A_A), DS52.7 (A_A), U5.14 (SEG_A)
/Display_management/SEG_A_MAX7221_3: DS9.7 (A_A), DS10.7 (A_A), DS11.7 (A_A), DS12.7 (A_A), DS53.7 (A_A), DS54.7 (A_A), DS55.7 (A_A), DS56.7 (A_A), U6.14 (SEG_A)
/Display_management/SEG_A_MAX7221_4: DS13.7 (A_A), DS14.7 (A_A), DS15.7 (A_A), DS16.7 (A_A), DS57.7 (A_A), DS58.7 (A_A), DS59.7 (A_A), DS60.7 (A_A), U7.14 (SEG_A)
/Display_management/SEG_A_MAX7221_5: DS17.7 (A_A), DS18.7 (A_A), DS19.7 (A_A), DS20.7 (A_A), DS61.7 (A_A), DS62.7 (A_A), DS63.7 (A_A), DS64.7 (A_A), U8.14 (SEG_A)
/Display_management/SEG_A_MAX7221_6: DS21.7 (A_A), DS22.7 (A_A), DS23.7 (A_A), DS24.7 (A_A), DS65.7 (A_A), DS66.7 (A_A), DS67.7 (A_A), DS68.7 (A_A), U9.14 (SEG_A)
/Display_management/SEG_A_MAX7221_7: DS25.7 (A_A), DS26.7 (A_A), DS27.7 (A_A), DS28.7 (A_A), DS69.7 (A_A), DS70.7 (A_A), DS71.7 (A_A), DS72.7 (A_A), U10.14 (SEG_A)
/Display_management/SEG_A_MAX7221_8: DS29.7 (A_A), DS30.7 (A_A), DS31.7 (A_A), DS32.7 (A_A), DS73.7 (A_A), DS74.7 (A_A), DS75.7 (A_A), DS76.7 (A_A), U11.14 (SEG_A)
/Display_management/SEG_A_MAX7221_9: DS33.7 (A_A), DS34.7 (A_A), DS35.7 (A_A), DS36.7 (A_A), U12.14 (SEG_A)
/Display_management/SEG_B_MAX7221_1: DS1.6 (A_B), DS2.6 (A_B), DS3.6 (A_B), DS4.6 (A_B), DS45.6 (A_B), DS46.6 (A_B), DS47.6 (A_B), DS48.6 (A_B), U4.16 (SEG_B)
/Display_management/SEG_B_MAX7221_2: DS5.6 (A_B), DS6.6 (A_B), DS7.6 (A_B), DS8.6 (A_B), DS49.6 (A_B), DS50.6 (A_B), DS51.6 (A_B), DS52.6 (A_B), U5.16 (SEG_B)
/Display_management/SEG_B_MAX7221_3: DS9.6 (A_B), DS10.6 (A_B), DS11.6 (A_B), DS12.6 (A_B), DS53.6 (A_B), DS54.6 (A_B), DS55.6 (A_B), DS56.6 (A_B), U6.16 (SEG_B)
/Display_management/SEG_B_MAX7221_4: DS13.6 (A_B), DS14.6 (A_B), DS15.6 (A_B), DS16.6 (A_B), DS57.6 (A_B), DS58.6 (A_B), DS59.6 (A_B), DS60.6 (A_B), U7.16 (SEG_B)
/Display_management/SEG_B_MAX7221_5: DS17.6 (A_B), DS18.6 (A_B), DS19.6 (A_B), DS20.6 (A_B), DS61.6 (A_B), DS62.6 (A_B), DS63.6 (A_B), DS64.6 (A_B), U8.16 (SEG_B)
/Display_management/SEG_B_MAX7221_6: DS21.6 (A_B), DS22.6 (A_B), DS23.6 (A_B), DS24.6 (A_B), DS65.6 (A_B), DS66.6 (A_B), DS67.6 (A_B), DS68.6 (A_B), U9.16 (SEG_B)
/Display_management/SEG_B_MAX7221_7: DS25.6 (A_B), DS26.6 (A_B), DS27.6 (A_B), DS28.6 (A_B), DS69.6 (A_B), DS70.6 (A_B), DS71.6 (A_B), DS72.6 (A_B), U10.16 (SEG_B)
/Display_management/SEG_B_MAX7221_8: DS29.6 (A_B), DS30.6 (A_B), DS31.6 (A_B), DS32.6 (A_B), DS73.6 (A_B), DS74.6 (A_B), DS75.6 (A_B), DS76.6 (A_B), U11.16 (SEG_B)
/Display_management/SEG_B_MAX7221_9: DS33.6 (A_B), DS34.6 (A_B), DS35.6 (A_B), DS36.6 (A_B), U12.16 (SEG_B)
/Display_management/SEG_C_MAX7221_1: DS1.4 (A_C), DS2.4 (A_C), DS3.4 (A_C), DS4.4 (A_C), DS45.4 (A_C), DS46.4 (A_C), DS47.4 (A_C), DS48.4 (A_C), U4.20 (SEG_C)
/Display_management/SEG_C_MAX7221_2: DS5.4 (A_C), DS6.4 (A_C), DS7.4 (A_C), DS8.4 (A_C), DS49.4 (A_C), DS50.4 (A_C), DS51.4 (A_C), DS52.4 (A_C), U5.20 (SEG_C)
/Display_management/SEG_C_MAX7221_3: DS9.4 (A_C), DS10.4 (A_C), DS11.4 (A_C), DS12.4 (A_C), DS53.4 (A_C), DS54.4 (A_C), DS55.4 (A_C), DS56.4 (A_C), U6.20 (SEG_C)
/Display_management/SEG_C_MAX7221_4: DS13.4 (A_C), DS14.4 (A_C), DS15.4 (A_C), DS16.4 (A_C), DS57.4 (A_C), DS58.4 (A_C), DS59.4 (A_C), DS60.4 (A_C), U7.20 (SEG_C)
/Display_management/SEG_C_MAX7221_5: DS17.4 (A_C), DS18.4 (A_C), DS19.4 (A_C), DS20.4 (A_C), DS61.4 (A_C), DS62.4 (A_C), DS63.4 (A_C), DS64.4 (A_C), U8.20 (SEG_C)
/Display_management/SEG_C_MAX7221_6: DS21.4 (A_C), DS22.4 (A_C), DS23.4 (A_C), DS24.4 (A_C), DS65.4 (A_C), DS66.4 (A_C), DS67.4 (A_C), DS68.4 (A_C), U9.20 (SEG_C)
/Display_management/SEG_C_MAX7221_7: DS25.4 (A_C), DS26.4 (A_C), DS27.4 (A_C), DS28.4 (A_C), DS69.4 (A_C), DS70.4 (A_C), DS71.4 (A_C), DS72.4 (A_C), U10.20 (SEG_C)
/Display_management/SEG_C_MAX7221_8: DS29.4 (A_C), DS30.4 (A_C), DS31.4 (A_C), DS32.4 (A_C), DS73.4 (A_C), DS74.4 (A_C), DS75.4 (A_C), DS76.4 (A_C), U11.20 (SEG_C)
/Display_management/SEG_C_MAX7221_9: DS33.4 (A_C), DS34.4 (A_C), DS35.4 (A_C), DS36.4 (A_C), U12.20 (SEG_C)
/Display_management/SEG_DP_MAX7221_1: DS1.5 (A_DP), DS2.5 (A_DP), DS3.5 (A_DP), DS4.5 (A_DP), DS45.5 (A_DP), DS46.5 (A_DP), DS47.5 (A_DP), DS48.5 (A_DP), U4.22 (SEG_DP)
/Display_management/SEG_DP_MAX7221_2: DS5.5 (A_DP), DS6.5 (A_DP), DS7.5 (A_DP), DS8.5 (A_DP), DS49.5 (A_DP), DS50.5 (A_DP), DS51.5 (A_DP), DS52.5 (A_DP), U5.22 (SEG_DP)
/Display_management/SEG_DP_MAX7221_3: DS9.5 (A_DP), DS10.5 (A_DP), DS11.5 (A_DP), DS12.5 (A_DP), DS53.5 (A_DP), DS54.5 (A_DP), DS55.5 (A_DP), DS56.5 (A_DP), U6.22 (SEG_DP)
/Display_management/SEG_DP_MAX7221_4: DS13.5 (A_DP), DS14.5 (A_DP), DS15.5 (A_DP), DS16.5 (A_DP), DS57.5 (A_DP), DS58.5 (A_DP), DS59.5 (A_DP), DS60.5 (A_DP), U7.22 (SEG_DP)
/Display_management/SEG_DP_MAX7221_5: DS17.5 (A_DP), DS18.5 (A_DP), DS19.5 (A_DP), DS20.5 (A_DP), DS61.5 (A_DP), DS62.5 (A_DP), DS63.5 (A_DP), DS64.5 (A_DP), U8.22 (SEG_DP)
/Display_management/SEG_DP_MAX7221_6: DS21.5 (A_DP), DS22.5 (A_DP), DS23.5 (A_DP), DS24.5 (A_DP), DS65.5 (A_DP), DS66.5 (A_DP), DS67.5 (A_DP), DS68.5 (A_DP), U9.22 (SEG_DP)
/Display_management/SEG_DP_MAX7221_7: DS25.5 (A_DP), DS26.5 (A_DP), DS27.5 (A_DP), DS28.5 (A_DP), DS69.5 (A_DP), DS70.5 (A_DP), DS71.5 (A_DP), DS72.5 (A_DP), U10.22 (SEG_DP)
/Display_management/SEG_DP_MAX7221_8: DS29.5 (A_DP), DS30.5 (A_DP), DS31.5 (A_DP), DS32.5 (A_DP), DS73.5 (A_DP), DS74.5 (A_DP), DS75.5 (A_DP), DS76.5 (A_DP), U11.22 (SEG_DP)
/Display_management/SEG_DP_MAX7221_9: DS33.5 (A_DP), DS34.5 (A_DP), DS35.5 (A_DP), DS36.5 (A_DP), U12.22 (SEG_DP)
/Display_management/SEG_D_MAX7221_1: DS1.2 (A_D), DS2.2 (A_D), DS3.2 (A_D), DS4.2 (A_D), DS45.2 (A_D), DS46.2 (A_D), DS47.2 (A_D), DS48.2 (A_D), U4.23 (SEG_D)
/Display_management/SEG_D_MAX7221_2: DS5.2 (A_D), DS6.2 (A_D), DS7.2 (A_D), DS8.2 (A_D), DS49.2 (A_D), DS50.2 (A_D), DS51.2 (A_D), DS52.2 (A_D), U5.23 (SEG_D)
/Display_management/SEG_D_MAX7221_3: DS9.2 (A_D), DS10.2 (A_D), DS11.2 (A_D), DS12.2 (A_D), DS53.2 (A_D), DS54.2 (A_D), DS55.2 (A_D), DS56.2 (A_D), U6.23 (SEG_D)
/Display_management/SEG_D_MAX7221_4: DS13.2 (A_D), DS14.2 (A_D), DS15.2 (A_D), DS16.2 (A_D), DS57.2 (A_D), DS58.2 (A_D), DS59.2 (A_D), DS60.2 (A_D), U7.23 (SEG_D)
/Display_management/SEG_D_MAX7221_5: DS17.2 (A_D), DS18.2 (A_D), DS19.2 (A_D), DS20.2 (A_D), DS61.2 (A_D), DS62.2 (A_D), DS63.2 (A_D), DS64.2 (A_D), U8.23 (SEG_D)
/Display_management/SEG_D_MAX7221_6: DS21.2 (A_D), DS22.2 (A_D), DS23.2 (A_D), DS24.2 (A_D), DS65.2 (A_D), DS66.2 (A_D), DS67.2 (A_D), DS68.2 (A_D), U9.23 (SEG_D)
/Display_management/SEG_D_MAX7221_7: DS25.2 (A_D), DS26.2 (A_D), DS27.2 (A_D), DS28.2 (A_D), DS69.2 (A_D), DS70.2 (A_D), DS71.2 (A_D), DS72.2 (A_D), U10.23 (SEG_D)
/Display_management/SEG_D_MAX7221_8: DS29.2 (A_D), DS30.2 (A_D), DS31.2 (A_D), DS32.2 (A_D), DS73.2 (A_D), DS74.2 (A_D), DS75.2 (A_D), DS76.2 (A_D), U11.23 (SEG_D)
/Display_management/SEG_D_MAX7221_9: DS33.2 (A_D), DS34.2 (A_D), DS35.2 (A_D), DS36.2 (A_D), U12.23 (SEG_D)
/Display_management/SEG_E_MAX7221_1: DS1.1 (A_E), DS2.1 (A_E), DS3.1 (A_E), DS4.1 (A_E), DS45.1 (A_E), DS46.1 (A_E), DS47.1 (A_E), DS48.1 (A_E), U4.21 (SEG_E)
/Display_management/SEG_E_MAX7221_2: DS5.1 (A_E), DS6.1 (A_E), DS7.1 (A_E), DS8.1 (A_E), DS49.1 (A_E), DS50.1 (A_E), DS51.1 (A_E), DS52.1 (A_E), U5.21 (SEG_E)
/Display_management/SEG_E_MAX7221_3: DS9.1 (A_E), DS10.1 (A_E), DS11.1 (A_E), DS12.1 (A_E), DS53.1 (A_E), DS54.1 (A_E), DS55.1 (A_E), DS56.1 (A_E), U6.21 (SEG_E)
/Display_management/SEG_E_MAX7221_4: DS13.1 (A_E), DS14.1 (A_E), DS15.1 (A_E), DS16.1 (A_E), DS57.1 (A_E), DS58.1 (A_E), DS59.1 (A_E), DS60.1 (A_E), U7.21 (SEG_E)
/Display_management/SEG_E_MAX7221_5: DS17.1 (A_E), DS18.1 (A_E), DS19.1 (A_E), DS20.1 (A_E), DS61.1 (A_E), DS62.1 (A_E), DS63.1 (A_E), DS64.1 (A_E), U8.21 (SEG_E)
/Display_management/SEG_E_MAX7221_6: DS21.1 (A_E), DS22.1 (A_E), DS23.1 (A_E), DS24.1 (A_E), DS65.1 (A_E), DS66.1 (A_E), DS67.1 (A_E), DS68.1 (A_E), U9.21 (SEG_E)
/Display_management/SEG_E_MAX7221_7: DS25.1 (A_E), DS26.1 (A_E), DS27.1 (A_E), DS28.1 (A_E), DS69.1 (A_E), DS70.1 (A_E), DS71.1 (A_E), DS72.1 (A_E), U10.21 (SEG_E)
/Display_management/SEG_E_MAX7221_8: DS29.1 (A_E), DS30.1 (A_E), DS31.1 (A_E), DS32.1 (A_E), DS73.1 (A_E), DS74.1 (A_E), DS75.1 (A_E), DS76.1 (A_E), U11.21 (SEG_E)
/Display_management/SEG_E_MAX7221_9: DS33.1 (A_E), DS34.1 (A_E), DS35.1 (A_E), DS36.1 (A_E), U12.21 (SEG_E)
/Display_management/SEG_F_MAX7221_1: DS1.9 (A_F), DS2.9 (A_F), DS3.9 (A_F), DS4.9 (A_F), DS45.9 (A_F), DS46.9 (A_F), DS47.9 (A_F), DS48.9 (A_F), U4.15 (SEG_F)
/Display_management/SEG_F_MAX7221_2: DS5.9 (A_F), DS6.9 (A_F), DS7.9 (A_F), DS8.9 (A_F), DS49.9 (A_F), DS50.9 (A_F), DS51.9 (A_F), DS52.9 (A_F), U5.15 (SEG_F)
/Display_management/SEG_F_MAX7221_3: DS9.9 (A_F), DS10.9 (A_F), DS11.9 (A_F), DS12.9 (A_F), DS53.9 (A_F), DS54.9 (A_F), DS55.9 (A_F), DS56.9 (A_F), U6.15 (SEG_F)
/Display_management/SEG_F_MAX7221_4: DS13.9 (A_F), DS14.9 (A_F), DS15.9 (A_F), DS16.9 (A_F), DS57.9 (A_F), DS58.9 (A_F), DS59.9 (A_F), DS60.9 (A_F), U7.15 (SEG_F)
/Display_management/SEG_F_MAX7221_5: DS17.9 (A_F), DS18.9 (A_F), DS19.9 (A_F), DS20.9 (A_F), DS61.9 (A_F), DS62.9 (A_F), DS63.9 (A_F), DS64.9 (A_F), U8.15 (SEG_F)
/Display_management/SEG_F_MAX7221_6: DS21.9 (A_F), DS22.9 (A_F), DS23.9 (A_F), DS24.9 (A_F), DS65.9 (A_F), DS66.9 (A_F), DS67.9 (A_F), DS68.9 (A_F), U9.15 (SEG_F)
/Display_management/SEG_F_MAX7221_7: DS25.9 (A_F), DS26.9 (A_F), DS27.9 (A_F), DS28.9 (A_F), DS69.9 (A_F), DS70.9 (A_F), DS71.9 (A_F), DS72.9 (A_F), U10.15 (SEG_F)
/Display_management/SEG_F_MAX7221_8: DS29.9 (A_F), DS30.9 (A_F), DS31.9 (A_F), DS32.9 (A_F), DS73.9 (A_F), DS74.9 (A_F), DS75.9 (A_F), DS76.9 (A_F), U11.15 (SEG_F)
/Display_management/SEG_F_MAX7221_9: DS33.9 (A_F), DS34.9 (A_F), DS35.9 (A_F), DS36.9 (A_F), U12.15 (SEG_F)
/Display_management/SEG_G_MAX7221_1: DS1.10 (A_G), DS2.10 (A_G), DS3.10 (A_G), DS4.10 (A_G), DS45.10 (A_G), DS46.10 (A_G), DS47.10 (A_G), DS48.10 (A_G), U4.17 (SEG_G)
/Display_management/SEG_G_MAX7221_2: DS5.10 (A_G), DS6.10 (A_G), DS7.10 (A_G), DS8.10 (A_G), DS49.10 (A_G), DS50.10 (A_G), DS51.10 (A_G), DS52.10 (A_G), U5.17 (SEG_G)
/Display_management/SEG_G_MAX7221_3: DS9.10 (A_G), DS10.10 (A_G), DS11.10 (A_G), DS12.10 (A_G), DS53.10 (A_G), DS54.10 (A_G), DS55.10 (A_G), DS56.10 (A_G), U6.17 (SEG_G)
/Display_management/SEG_G_MAX7221_4: DS13.10 (A_G), DS14.10 (A_G), DS15.10 (A_G), DS16.10 (A_G), DS57.10 (A_G), DS58.10 (A_G), DS59.10 (A_G), DS60.10 (A_G), U7.17 (SEG_G)
/Display_management/SEG_G_MAX7221_5: DS17.10 (A_G), DS18.10 (A_G), DS19.10 (A_G), DS20.10 (A_G), DS61.10 (A_G), DS62.10 (A_G), DS63.10 (A_G), DS64.10 (A_G), U8.17 (SEG_G)
/Display_management/SEG_G_MAX7221_6: DS21.10 (A_G), DS22.10 (A_G), DS23.10 (A_G), DS24.10 (A_G), DS65.10 (A_G), DS66.10 (A_G), DS67.10 (A_G), DS68.10 (A_G), U9.17 (SEG_G)
/Display_management/SEG_G_MAX7221_7: DS25.10 (A_G), DS26.10 (A_G), DS27.10 (A_G), DS28.10 (A_G), DS69.10 (A_G), DS70.10 (A_G), DS71.10 (A_G), DS72.10 (A_G), U10.17 (SEG_G)
/Display_management/SEG_G_MAX7221_8: DS29.10 (A_G), DS30.10 (A_G), DS31.10 (A_G), DS32.10 (A_G), DS73.10 (A_G), DS74.10 (A_G), DS75.10 (A_G), DS76.10 (A_G), U11.17 (SEG_G)
/Display_management/SEG_G_MAX7221_9: DS33.10 (A_G), DS34.10 (A_G), DS35.10 (A_G), DS36.10 (A_G), U12.17 (SEG_G)
/MOSI_MAX7221_5V: U4.1 (DIN); also elsewhere on the board
/SCK_MAX7221_5V: U4.13 (CLK), U5.13 (CLK), U6.13 (CLK), U7.13 (CLK), U8.13 (CLK), U9.13 (CLK), U10.13 (CLK), U11.13 (CLK), U12.13 (CLK); also elsewhere on the board
GND: C14.2, C15.2, C16.2, C17.2, C18.2, C19.2, C20.2, C21.2, C22.2, U4.4 (GND), U4.9 (GND), U5.4 (GND), U5.9 (GND), U6.4 (GND), U6.9 (GND), U7.4 (GND), U7.9 (GND), U8.4 (GND), U8.9 (GND), U9.4 (GND), U9.9 (GND), U10.4 (GND), U10.9 (GND), U11.4 (GND), U11.9 (GND), U12.4 (GND), U12.9 (GND); also elsewhere on the board
unnamed: TP8.1 (1_1), U4.24 (DOUT), U5.1 (DIN)
unnamed: R12.2, U4.18 (ISET)
unnamed: U5.24 (DOUT), U6.1 (DIN)
unnamed: R13.2, U5.18 (ISET)
unnamed: U6.24 (DOUT), U7.1 (DIN)
unnamed: R14.2, U6.18 (ISET)
unnamed: U7.24 (DOUT), U8.1 (DIN)
unnamed: R15.2, U7.18 (ISET)
unnamed: U8.24 (DOUT), U9.1 (DIN)
unnamed: R16.2, U8.18 (ISET)
unnamed: R17.2, U9.18 (ISET)
unnamed: U9.24 (DOUT), U10.1 (DIN)
unnamed: U10.24 (DOUT), U11.1 (DIN)
unnamed: R18.2, U10.18 (ISET)
unnamed: TP15.1 (1_1), U11.24 (DOUT), U12.1 (DIN)
unnamed: R19.2, U11.18 (ISET)
unnamed: R20.2, U12.18 (ISET)
