JoseSanchez122/MULTI_TIMERS_CALIBRATOR/Hardware_design/Hardware_design.kicad_pcb

## KiCad design Hardware_design/Hardware_design.kicad_pcb (continued)

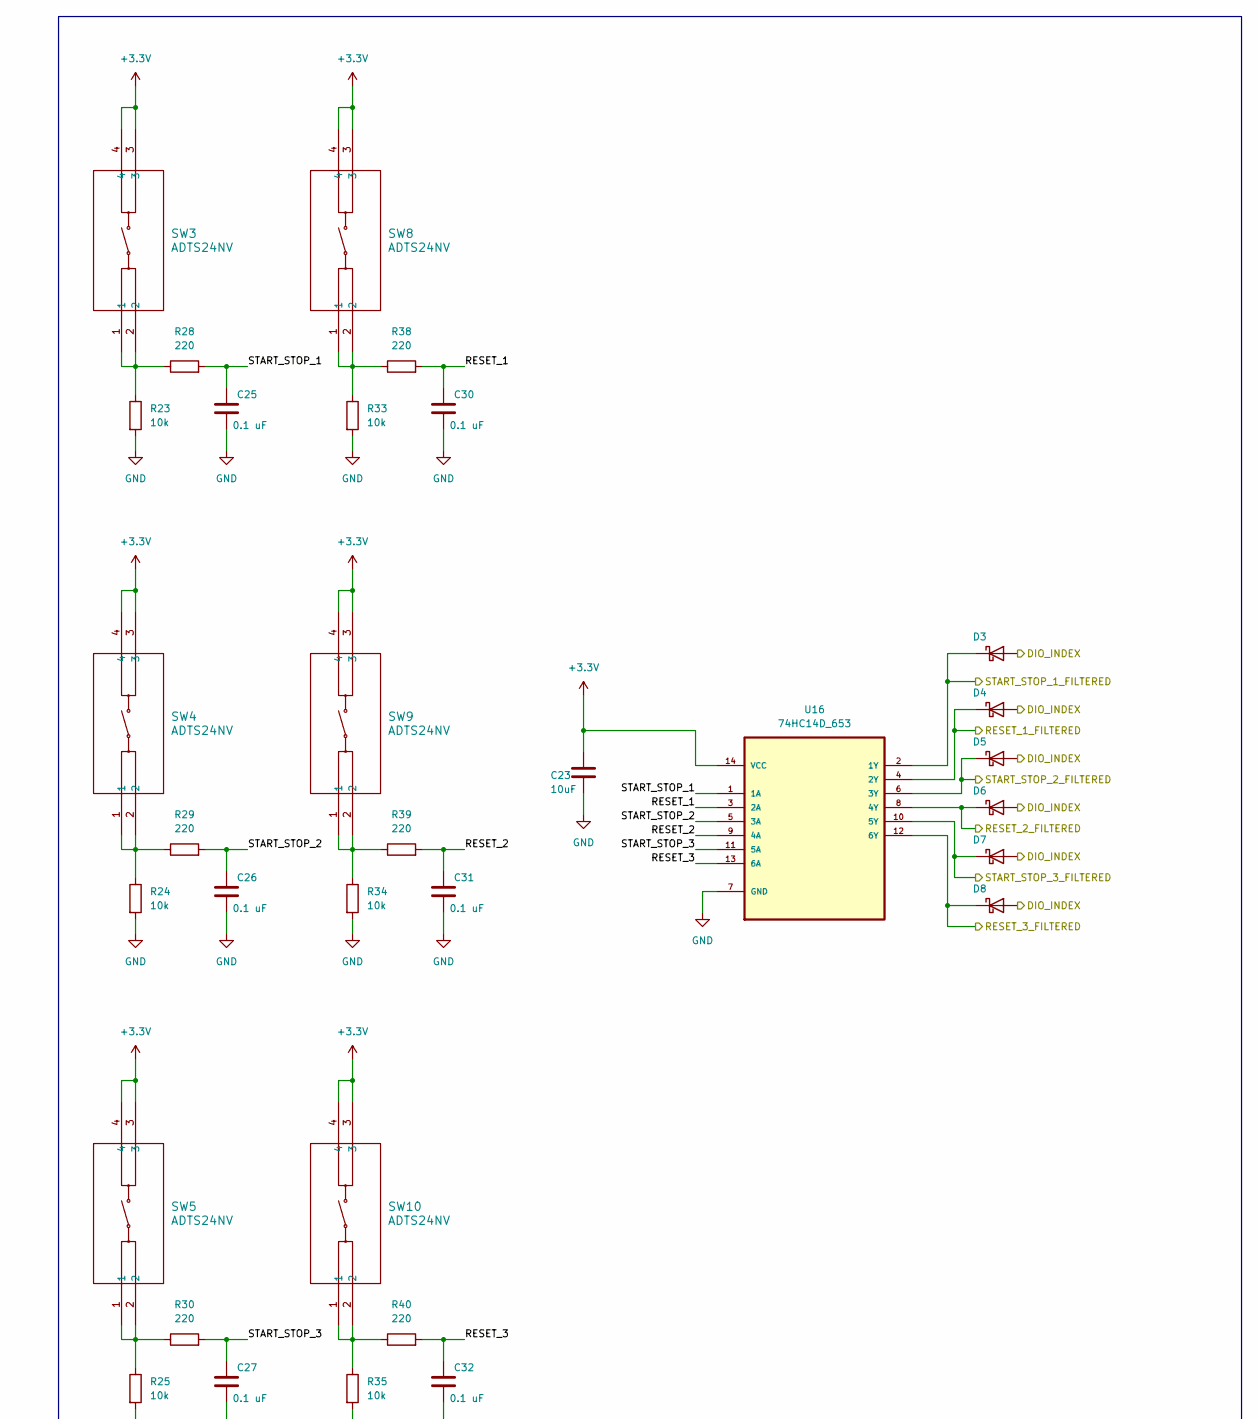
[picture p29: schematic Buttons_circuits.kicad_sch, part in row 1, column 1]

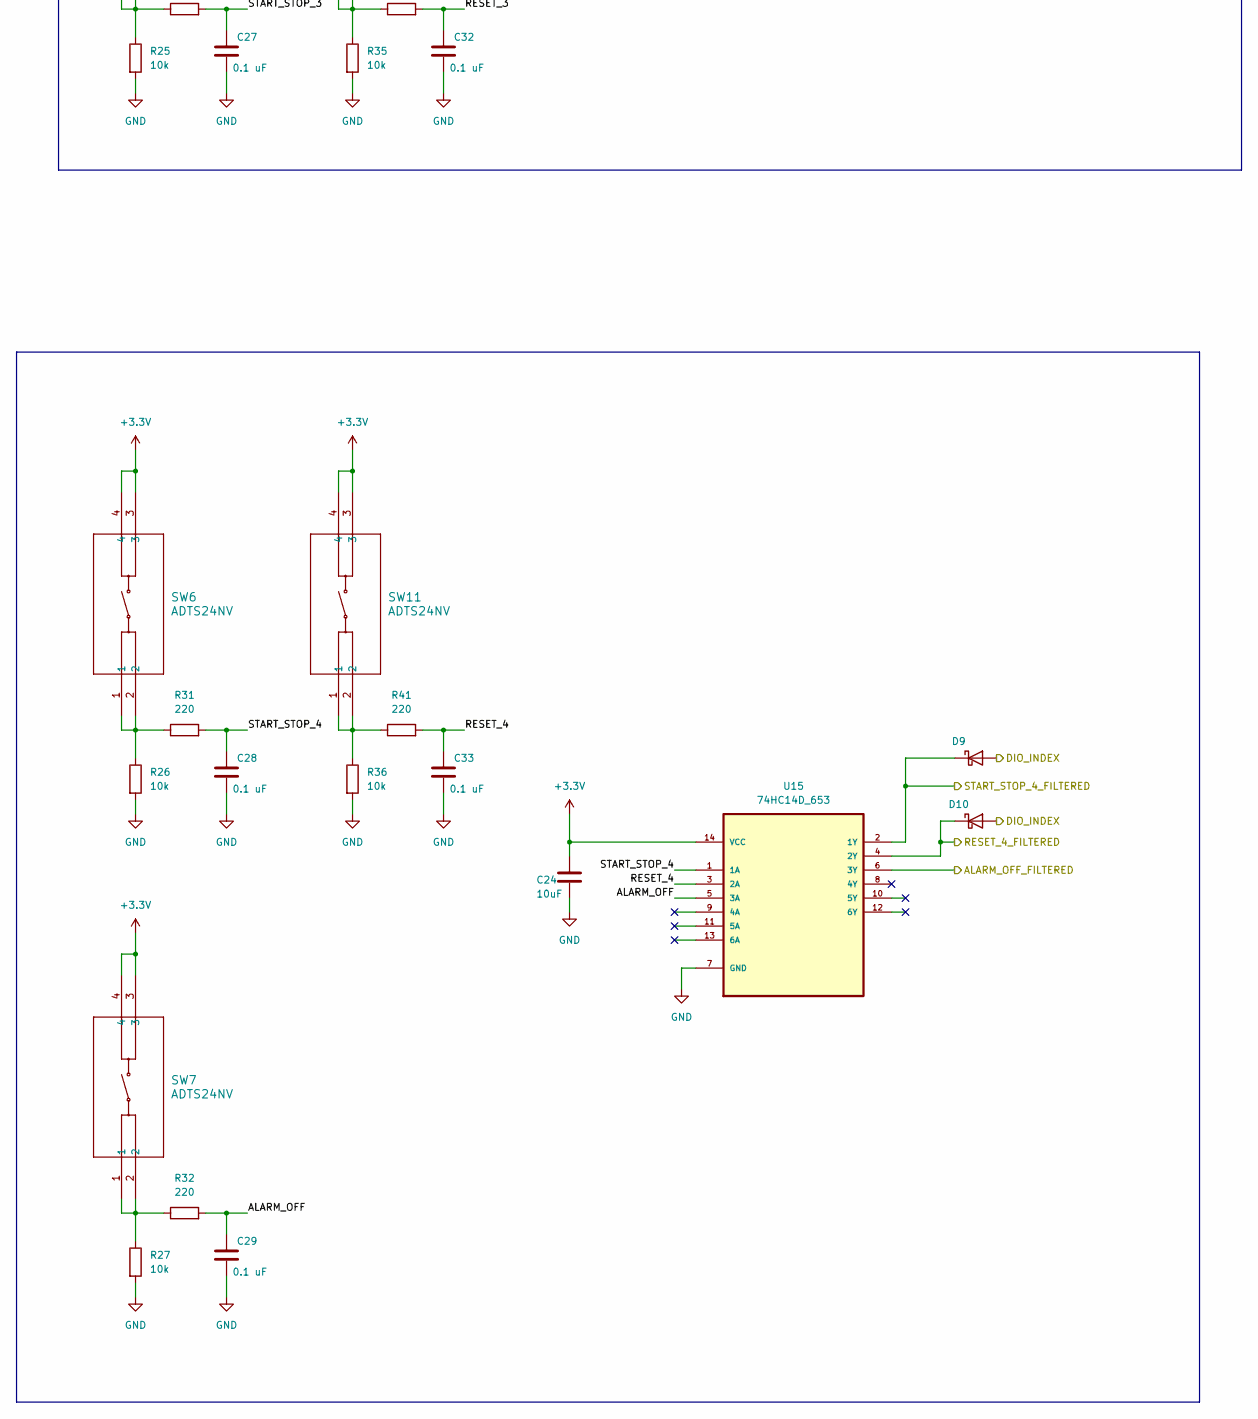
[picture p30: schematic Buttons_circuits.kicad_sch, part in row 2, column 1]

Parts:
C23, C24: 10uF; 0805_SMD_TANT_CAP_T491B106K016AT
C25, C26, C27, C28, C29, C30, C31, C32, C33: 0.1 uF; 0805_SMD_CERAMIC_CAP_T491B106K016AT
D3, D4, D5, D6, D7, D8, D9, D10: D_Schottky; DIO_Schottky _MBR0530T3G
R23, R24, R25, R26, R27, R33, R34, R35, R36: 10k; 0805_RES_RESC2012X60N
R28, R29, R30, R31, R32, R38, R39, R40, R41: 220; 0805_RES_RESC2012X60N
SW3, SW4, SW5, SW6, SW7, SW8, SW9, SW10, SW11: ADTS24NV; PUSH_BUTTON_ADTS24NV
U15, U16: 74HC14D_653; Schimitt_Trigger_74HC14D_653; MPN 74HCT14D,653

Connections:
+3.3V: C23.1, C24.1, SW3.3, SW3.4, SW4.3, SW4.4, SW5.3, SW5.4, SW6.3, SW6.4, SW7.3, SW7.4, SW8.3, SW8.4, SW9.3, SW9.4, SW10.3, SW10.4, SW11.3, SW11.4, U15.14 (VCC), U16.14 (VCC); also elsewhere on the board
/Alarm_OFF_FILTERED: U15.6 (3Y); also elsewhere on the board
/Buttons_circuits/ALARM_OFF: C29.1, R32.2, U15.5 (3A)
/Buttons_circuits/RESET_1: C30.1, R38.2, U16.3 (2A)
/Buttons_circuits/RESET_2: C31.1, R39.2, U16.9 (4A)
/Buttons_circuits/RESET_3: C32.1, R40.2, U16.13 (6A)
/Buttons_circuits/RESET_4: C33.1, R41.2, U15.3 (2A)
/Buttons_circuits/START_STOP_1: C25.1, R28.2, U16.1 (1A)
/Buttons_circuits/START_STOP_2: C26.1, R29.2, U16.5 (3A)
/Buttons_circuits/START_STOP_3: C27.1, R30.2, U16.11 (5A)
/Buttons_circuits/START_STOP_4: C28.1, R31.2, U15.1 (1A)
/INDEX: D3.A, D4.A, D5.A, D6.A, D7.A, D8.A, D9.A, D10.A; also elsewhere on the board
/RESET_1_FILTERED: D4.C (K), U16.4 (2Y); also elsewhere on the board
/RESET_2_FILTERED: D6.C (K), U16.8 (4Y); also elsewhere on the board
/RESET_3_FILTERED: D8.C (K), U16.12 (6Y); also elsewhere on the board
/RESET_4_FILTERED: D10.C (K), U15.4 (2Y); also elsewhere on the board
/START_STOP_1_FILTERED: D3.C (K), U16.2 (1Y); also elsewhere on the board
/START_STOP_2_FILTERED: D5.C (K), U16.6 (3Y); also elsewhere on the board
/START_STOP_3_FILTERED: D7.C (K), U16.10 (5Y); also elsewhere on the board
/START_STOP_4_FILTERED: D9.C (K), U15.2 (1Y); also elsewhere on the board
GND: C23.2, C24.2, C25.2, C26.2, C27.2, C28.2, C29.2, C30.2, C31.2, C32.2, C33.2, R23.2, R24.2, R25.2, R26.2, R27.2, R33.2, R34.2, R35.2, R36.2, U15.7 (GND), U16.7 (GND); also elsewhere on the board
unnamed: R23.1, R28.1, SW3.1, SW3.2
unnamed: R24.1, R29.1, SW4.1, SW4.2
unnamed: R25.1, R30.1, SW5.1, SW5.2
unnamed: R26.1, R31.1, SW6.1, SW6.2
unnamed: R27.1, R32.1, SW7.1, SW7.2
unnamed: R33.1, R38.1, SW8.1, SW8.2
unnamed: R34.1, R39.1, SW9.1, SW9.2
unnamed: R35.1, R40.1, SW10.1, SW10.2
unnamed: R36.1, R41.1, SW11.1, SW11.2

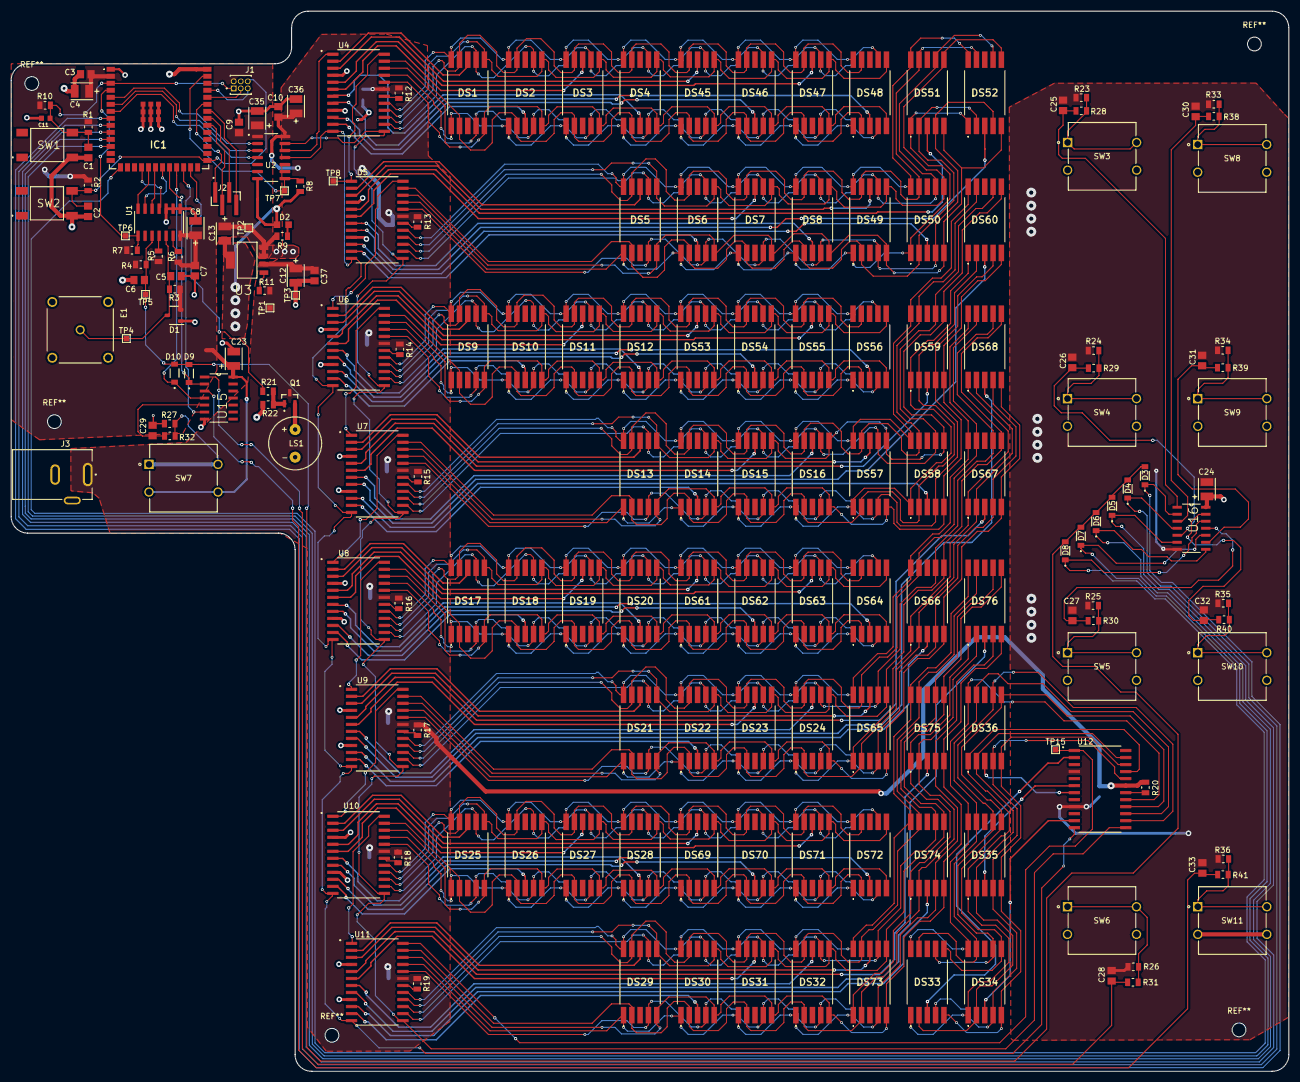
[picture p31: board Hardware_design.kicad_pcb from above]

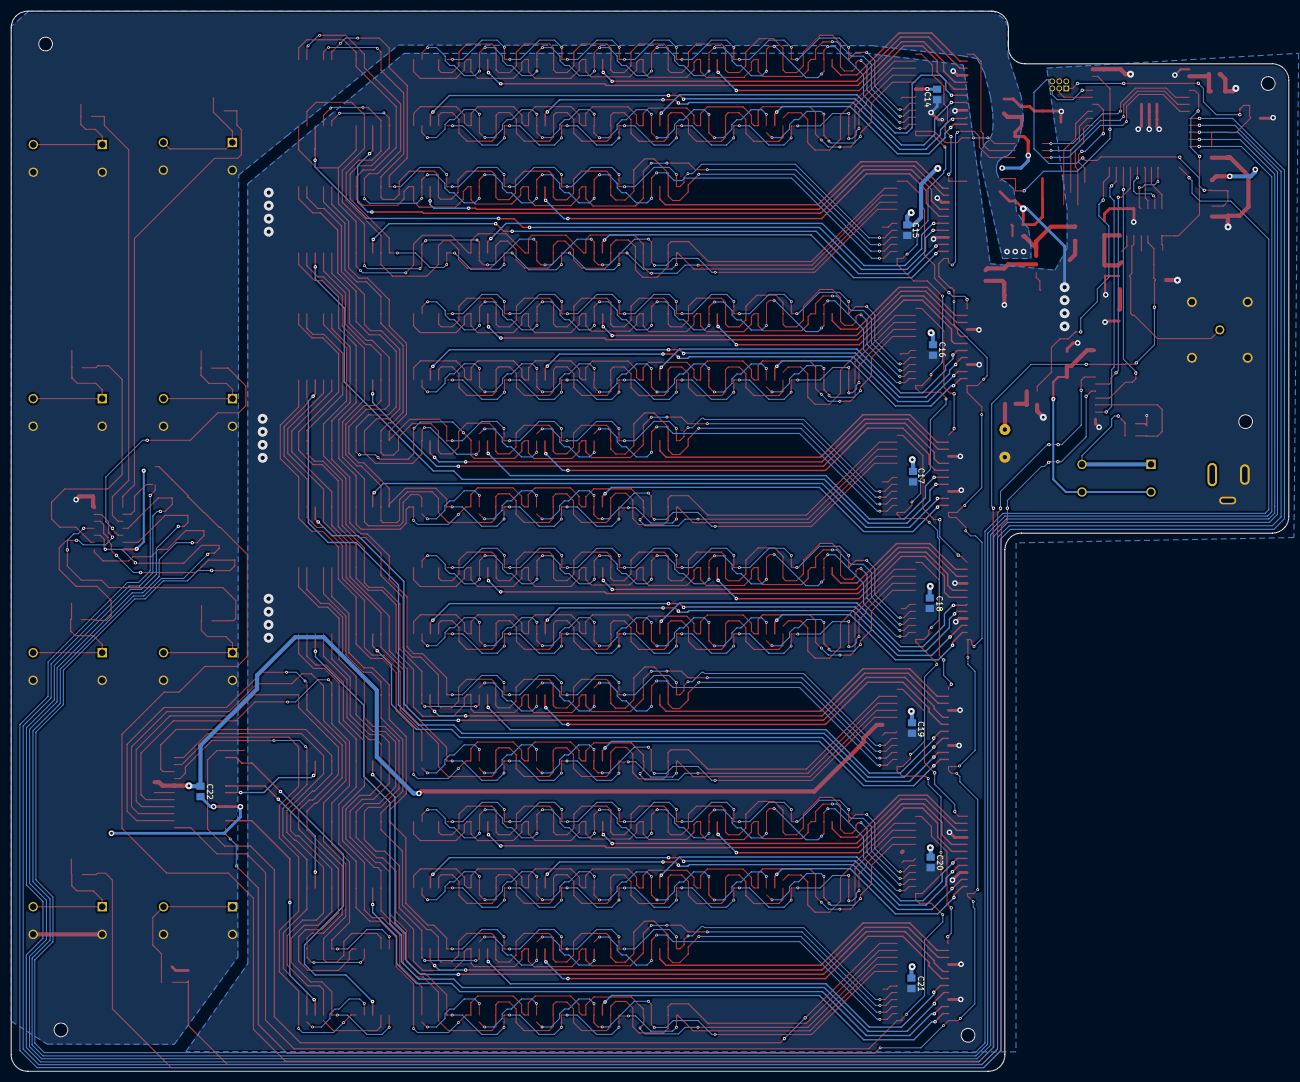
[picture p32: board Hardware_design.kicad_pcb from below]

Board: 2 copper layers, 231.3 x 191.9 mm, 195 parts (9 on the bottom side), 216 nets.
