JoseSanchez122/MULTI_TIMERS_CALIBRATOR/Frimware_tests/GPIO_AND_INTERRUPT_TEST/main/main.c

#include <stdio.h>
#include "driver/gpio.h"
#include "freertos/FreeRTOS.h"
#include "freertos/task.h"
#include "esp_task_wdt.h"

#define LFLAG_PIN GPIO_NUM_5

// Variable para detectar la interrupción
volatile BaseType_t  interrupcion_ocurrio = false;

// ISR (se ejecuta cuando el pin cambia de HIGH a LOW)
static void IRAM_ATTR isr_handler(void *arg)
{
    if (gpio_get_level(LFLAG_PIN) == 0){
        interrupcion_ocurrio = true;
    }
}

void app_main(void)
{
    ESP_ERROR_CHECK( esp_task_wdt_deinit() );
    // Configurar el pin como entrada con pull-up
    gpio_config_t io_conf = {
        .pin_bit_mask = (1ULL << LFLAG_PIN),
        .mode = GPIO_MODE_INPUT,
        .pull_up_en = GPIO_PULLUP_DISABLE,
        .pull_down_en = GPIO_PULLDOWN_DISABLE,
        .intr_type = GPIO_INTR_NEGEDGE,  
    };
    gpio_config(&io_conf);
    
    // Instalar el servicio de interrupciones
    gpio_install_isr_service(ESP_INTR_FLAG_IRAM);
    
    // Asignar el handler al pin
    gpio_isr_handler_add(LFLAG_PIN, isr_handler, NULL);
    
    int num = 0;
    // Loop infinito 
    while (1) {
        
        // int nivel = gpio_get_level(LFLAG_PIN);
        // if (nivel == 0) {
        //     printf("Pin en BAJO (0)\n");
        // } else {
        //     printf("Pin en ALTO (1)\n");
        // }
        
        if (interrupcion_ocurrio) {
            printf("DETECTADA! %d \n", num++);
            interrupcion_ocurrio = false;
            
        }
        
        vTaskDelay(pdMS_TO_TICKS(100));  // Pequeña pausa para no saturar
    }
}
