JoseSanchez122/MULTI_TIMERS_CALIBRATOR/Frimware_tests/sample_project/main/main.c

#include <stdio.h>
#include "driver/gpio.h"
#include "freertos/FreeRTOS.h"

#define led_pin 2

void app_main(void)
{
    gpio_reset_pin(led_pin);
    gpio_set_direction(led_pin, GPIO_MODE_OUTPUT);

    while(1){
        gpio_set_level(led_pin, true);
        vTaskDelay(500/portTICK_PERIOD_MS);

        gpio_set_level(led_pin, false);
        vTaskDelay(500/portTICK_PERIOD_MS);
    }

}
